KasperBaun/RabbitHouse/docs/løbegård/fundament.md

# Fundament — Løbegård

> Implementeret i `src/designs/yard/foundation.scad`.

Løbegård-fundamentet er en fundablok-ring under løbegårdens 3 ydervægge
(V1 front, V2 bag, V5 højre), lagt i **halvstensforbandt med vekslende
hjørne-ejerskab** — samme mønster som [hus-fundamentet](../hus/fundament.md).

I **kombineret build** med hus'et danner hus'ets V4-væg (ved X = 2000)
løbegårdens venstre side — så løbegårdens egen ring har KUN 3 sider. I
**standalone-build** (`standalone = true`) renderes også en venstre strip
ved X = hl så løbegården står alene.

Ringen er 4000 × 2000 mm udvendigt (yard sidder ved Y = 1000..3000 så hus'ets
front rager 1000 mm forbi yard-fronten) og 80 cm høj (4 skifter à 20 cm).
12 cm sokkel over jord, 68 cm under jord — samme dybde som hus-fundamentet.

```
        Y
        ↑
   Y=3000 ┌─────────────────────────────────────────┐  ← V2 bag (yard-segment)
          │                                         │
          │                                         │V5
          │       Løbegård X = 2000..6000           │  ← 2000 mm
          │       Y = 1000..3000                    │    (V5 højre)
          │                                         │
          │       (V4 = husets højre væg → fælles)  │
   Y=1000 └─────────────────────────────────────────┘  ← V1 front (yard-segment)
          X=2000                                X=6000
                       4000 mm
                  (V1, V2 yard-segment)
                  (set ovenfra)
```

## Mål

| Egenskab | Værdi |
|---|---|
| Løbegård-footprint udvendigt | 4000 × 2000 mm (X = 2000..6000, Y = 1000..3000) |
| Antal skifter | 4 |
| Total ringhøjde | 800 mm (4 × 200) |
| Sokkel-højde over jord | 120 mm (Z = +120 mm = RH_BASE_H) |
| Buried dybde | 680 mm |
| Fundablok dim. | 500 × 150 × 200 mm |
| Stabilgrus i bunden | 100 mm |
| Total grøftedybde | ~80 cm (680 ring + 100 grus) |
| Venstre væg (V4) | I COMBINED: ejet af hus. I STANDALONE: render egen strip |

## Halvstensforbandt — hjørner skifter ejer per skifte

Hjørnerne ved V5 (front-right og back-right) interlocker perpendikulært
mellem skifter — samme princip som hus'ets fundament, men her er det de
**lange vægge** (V1 og V2, 4000 mm) der ejer hjørnerne på ulige skifter, og
den **korte væg** (V5 — 2000 mm, fordi yard-dybden Y = 1000..3000) der ejer
hjørnerne på lige skifter.

| Skifte | Lange vægge (V1, V2 — 4000 mm) | Kort væg (V5 — 2000 mm) |
|---|---|---|
| Lige (0, 2)  | Mellem: X = 2000..5850 (8 blokke: 7×500 + 350 cut) | Fuld: Y = 1000..3000 (4 × 500) |
| Ulige (1, 3) | Fuld: X = 2000..6000 (8 × 500) | Mellem: Y = 1150..2850 (4 blokke: 3×500 + 200 cut) |

**Combined pr. skifte** = 8 + 8 + 4 = **20 blokke**.
4 skifter × 20 = **80 blokke** netto.

I STANDALONE-mode tilføjes V4 venstre væg (samme dimensioner som V5 — kort,
2000 mm): den ejer hjørner sammen med V5 på lige skifter, og sidder mellem
på ulige. Det giver 24 blokke pr. skifte × 4 = **96 blokke** standalone.

## Konstruktion — tværsnit

```
                            ↓ M10 ankerskrue c/c 1000 mm i topskiftet
        ┌────────────────────────────────────┐    ← sokkel z = +120 mm
        │            4. skifte               │
        │ - - - - - - - - - - - - - - - - -  │    ← grade z = 0 (jord/græs)
        ├────────────────────────────────────┤    ← z = −80 mm
        │            3. skifte               │
        ├────────────────────────────────────┤    ← z = −280 mm
        │            2. skifte               │
        ├────────────────────────────────────┤    ← z = −480 mm
        │            1. skifte               │
        └────────────────────────────────────┘    ← z = −680 mm
        ░░░░░░░░░ stabilgrus 100 mm ░░░░░░░░░░
        ─────────────────────────────────────    ← z = −780 mm (bund af grøft)
                       (snit gennem yard-væg)
```

Hulrum udstøbes med selvblandet beton (cement + støbemix + vand, ~1:4).
Topskiftet ligger flush med sokkel-niveau (z = +120 mm).

**Armering (Ø10 mm kamstål):**

| Placering | Antal stænger | Bemærk |
|---|---|---|
| 1. skifte (bund) | **2 stænger** vandret hele 3-sidet perimeter rundt | Lægges i hulrum før udstøbning |
| 4. skifte (top) | **2 stænger** vandret hele 3-sidet perimeter rundt | Lægges før topudstøbning, før ankerskruerne bores |
| Lodret | **4–6 stk** korte stænger (~600 mm) | I V5-hjørner + et par midt på V1/V2 — bindes til top og bund banderne |

Perimeter (3-sidet) = 4000 + 2000 + 4000 = 10 m. Per band kræves ceil(10/3) = 4
stk 3 m-stænger med overlap ~400 mm i midten af V1/V2. ALDRIG overlap i et hjørne.

M10 ankerskruer drives ned i topskiftet c/c 1000 mm. Ankeren ved X = 2000
(grænse mod hus) ejes af [hus-fundamentet](../hus/fundament.md) — yard
starter sine egne ankre ved X = 2500.

## Materialeliste — løbegård (combined mode)

| # | Vare | Beskrivelse | Antal | Enhed |
|---|---|---|---|---|
| 1 | Stabilgrus 0–32 mm | Bundlag 100 mm i frostfri grøft (~10 m perimeter × 30 cm × 10 cm) | ~0,30 | m³ (~510 kg) |
| 2 | Fundablok 50 × 20 × 15 cm | 4 skifter halvstensforbandt på 3-sidet ring (V4 er hus'ets) | 86 | stk (80 + 6 buffer) |
| 3 | Kamstål Ø10 mm × 3 m | 2 bund (8 stk for 10 m) + 2 top (8 stk). Lodrette stykker = genbrug af egne metalstænger | 16 | stk |
| 4 | Cement (Aalborg Portland CEM I/II, 25 kg-sæk) | Hulrumsudstøbning ~300 L beton ved 1:4 | 10 | sæk |
| 5 | Støbemix 0–16 mm | Sand+grus til selvblanding | ~625 | kg |
| 6 | Ankerskruer M10 × 120 | Bundrem-til-ring: 4 på V1, 4 på V2, 2 på V5 | 10 | stk |

> Priser pr. enhed slås op i [materialeliste.xlsx](../materialeliste.xlsx),
> Zone-kolonne = "Yard".

### Standalone-tillæg

Hvis løbegården bygges helt for sig selv (ingen hus), tilføj:

| Tilføjelse | Antal | Note |
|---|---|---|
| Fundablok extra | +16 stk | Venstre strip ved X = 2000 (4 skifter × 4 blokke; V4 = 2000 mm) |
| Kamstål Ø10 mm × 3 m extra | +2 stk | V4-bane: 1 bund + 1 top à 2 m (lodret = genbrug egne stænger) |
| Cement extra | +2 sæk | Ekstra hulrum (~60 L beton) |
| Stabilgrus extra | ~100 kg | Ekstra V4-grøft 2 m × 30 cm × 10 cm |
| Ankerskruer M10 extra | +2 stk | V4 venstre væg (Y = 1500, 2500) |

## Bygge-rækkefølge

1. Mark op yard-hjørner ved (2000, 0), (6000, 0), (6000, 3000), (2000, 3000).
   (Standalone: marker også ny væg-linje ved X = 2000.)
2. Udgrav rendegrøft ~30 cm bred × ~80 cm dyb langs V1 (front), V2 (bag) og
   V5 (højre). Standalone: også langs V4 (venstre).
3. Læg 100 mm stabilgrus i bunden, komprimer.
4. Læg **1. skifte** (ulige — V1, V2 ejer hjørner): V1 og V2 fuld X = 2000..6000,
   V5 mellem Y = 1150..2850. Standalone: V4 også mellem Y = 1150..2850.
5. **Læg 2 stk Ø10 mm kamstål vandret** i hulrummet i 1. skifte hele
   3-sidet perimeter rundt. Overlap ~400 mm midt på V1/V2; aldrig over hjørne.
6. Læg **2. skifte** (lige — V5 ejer hjørner): V5 fuld Y = 1000..3000. V1 og V2
   mellem X = 2000..5850. Standalone: V4 også fuld Y = 1000..3000.
7. **Sæt 4–6 lodrette Ø10 mm-stykker (~600 mm)** ned gennem hulrum i V5-
   hjørner + midt på V1, V2 — bindes til bund-banerne.
8. Læg **3. skifte** (ulige — samme som 1.).
9. Læg **4. skifte** (lige — samme som 2.).
10. **Læg 2 stk Ø10 mm kamstål vandret** i hulrummet i 4. skifte; bindes
    til de lodrette.
11. Bland beton (cement + støbemix + vand ~1:4), udstøb alle hulrum.
    Lad hærde ~7 dage.
12. Bor og sæt M10 ankerskruer c/c 1000 mm i topskiftet:
    - V1 (front): x = 2500, 3500, 4500, 5500 (4 stk; c/c 1000 fra x = 2500)
    - V2 (bag): x = 2500, 3500, 4500, 5500
    - V5 (højre): y = 1500, 2500 (2 stk; yard-dybde 2000 mm rummer kun 2)
    - Standalone V4 (venstre): y = 1500, 2500

## Rendering / verificering

```powershell
# Render combined build (hus + yard) for at se hvordan yard's fundament
# slutter op mod hus'ets V4 ved X = 2000.
& "C:\Program Files\OpenSCAD\openscad.exe" `
    -o _renders/yard_fundament.png --imgsize=1000,600 `
    --camera=3000,1500,-200,75,0,30,16000 `
    src/main.scad
```

Inspect:
- Yard's V1 og V2 starter ved X = 2000 (mod hus) og går til X = 6000
- V5 højre fundament løber fra Y = 1000 til Y = 3000 i lige skifter,
  fra Y = 1150 til Y = 2850 i ulige skifter (interlocker med V1/V2)
- I COMBINED ingen venstre væg (V4 er hus'ets); i STANDALONE er der egen V4-strip
  med samme alternation som V5
- Topskifte flush med sokkel-niveau (Z = +120 mm), 4 skifter (80 cm) dybt
- M10 ankerskruer (10 stk i combined; 12 i standalone) i topskiftet
