KasperBaun/RabbitHouse/docs/arbejdsplan/lem-og-trappe.md

# Lem & trappe — byg med det træ du har

> De to sværeste ting i gulvet. **Hvor** lemmene sidder står i
> **[gulvkonstruktion-braedder.md](gulvkonstruktion-braedder.md)** — her er **hvordan** du bygger dem.
> Hele guiden er skrevet til **genbrugstræ**: du køber ikke krydsfiner eller brede
> planker, du **måler og skærer på stedet** ud fra det du finder. Alm. gran —
> **ikke trykimprægneret**. Byg typisk **trapperne først**, lemmene til sidst.

## Kan jeg bruge dette stykke træ?

Du behøver ikke regne baglæns. Hold stykket op mod tabellen — passer det med
minimumskravet til en rolle, kan du bruge det:

| Rolle | Min. tykkelse | Min. bredde/dybde | Længde du skal bruge | Ideelt / noter |
|---|---|---|---|---|
| **Trin** | ~22 mm (helst 40–45) | **~9–10 cm** (det er trin-dybden — en fod skal kunne stå) | **55 cm** pr. trin (= trappebredden) | **Reglar 45×95 lagt fladt er perfekt.** 5 trin pr. trappe |
| **Vange** (side) | ~30 mm (helst 45) | **~95 mm** (helst 120–160 for stivhed over ~1 m) | start med **≥ 110 cm** rå, skæres til | 2 vanger pr. trappe |
| **Låg-brædt** | = gulvbræddet (~25 mm) | hvad som helst | nok til at dække åbningen | brug **rester af gulvbrædderne** så låget flugter dækket |
| **Tværrevle** (under låg) | ~30 mm | ~45 mm | passer inden for det frie hul | 2–3 pr. låg. ~45×45 er fint |
| **Fals-liste** | ~30 mm | ~45 mm | hele åbningens omkreds | ~45×45. Hyldekant låget hviler på |

Er et bræt for smalt til en vange, men tykt nok? → brug det som trin eller revle.
Intet går til spilde.

---

# DEL A — Lemmen (× 2)

Lemmen er et **udtageligt/hængslet stykke gulv** i samme tykkelse som dækket, så
den flugter. To ting afgør det: en **fals** den hviler på, og et **greb** den
løftes i. Låget bygger du selv af gulvbræt-rester — **ingen krydsfiner.**

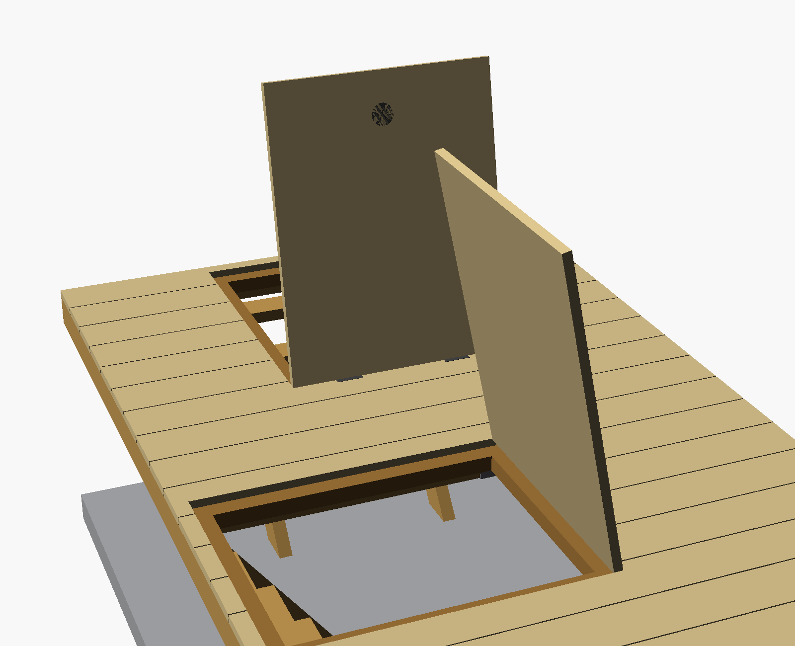
[picture p2: docs/arbejdsplan/img/lem-3d.png]
Lem — fals + greb, vist åben


*Begge låg vist åbne. Orange inderkant i åbningen = **falsen**. Ringen på
låg-oversiden = **grebet**.*

## A1 · Marker og skær åbningen

Mål fra dækkets forreste venstre hjørne (se gulv-guiden):

| Lem | Fra venstre (X) | Fra forkant (Y) | Størrelse |
|---|---|---|---|
| LEM 1 | **50,0 cm** | **4,5 cm** | 70 × 90 cm |
| LEM 2 | **75,5 cm** | **143,5 cm** | 90 × 70 cm |

1. Afsæt de 4 hjørner, slå rette vinkler med **3-4-5** (30-40-50 cm).
2. Skær med stiksav langs stregen.
3. **Tjek støtten:** hver kant skal hvile på en regel/veksel at skrue dæk + fals i.
   Mangler der støtte langs en kant (fordi bærereglarne ikke ligger som planlagt),
   så skru en **ekstra veksel 45×95** ind langs kanten først.

## A2 · Falsen — så låget ikke kan falde ned

Søm/skru **fals-liste ~45×45 hele vejen rundt på indersiden** af åbningen, med
**overkant 2,5 cm under dæk-overkant** (= i niveau med dæk-undersiden). Listen
rager ~5 cm ind og danner en hylde. Låget lægges ned i den 2,5 cm dybe fals og
**flugter dækket** — det er større end det frie hul og kan ikke falde igennem.

```
   (gulv-side)                          (åbning / kælder)
   dæk 25 ───────┐   ~0,5 cm luft  ┌─────── låg 25 mm ─────────
   z12 .........│...............│.....................  ← overkant flugter dæk
   z9,5 ────────┤▓▓▓▓▓▓▓▓▓▓▓▓▓▓│  låget hviler på falsen
   ramme-regel  │  fals-liste  │
   45×95        │ ~45×45       │
   z0  ─────────┘              └──────  ▼  frit hul ned til trappen
```

## A3 · Byg låget af gulvbræt-rester (~0,5 cm luft hele vejen)

| Lem | Åbning | **Låg (færdigt mål)** |
|---|---|---|
| LEM 1 | 70 × 90 cm | **~69,5 × 89,5 cm** |
| LEM 2 | 90 × 70 cm | **~89,5 × 69,5 cm** |

1. Læg **rester af gulvbrædderne side om side**, til de dækker åbningen, og skær
   dem så hele låget bliver ~0,5 cm mindre end åbningen i begge retninger.
2. Skru **2–3 tværrevler (~45×45) på undersiden, på tværs af bræddesamlingerne** —
   de holder brædderne sammen til ét stykke **og** afstiver mod en voksen-fod.
3. Placér revlerne **inden for det frie hul** (ikke under falsen) — så de stikker
   ned i hullet og **låser samtidig låget mod at skride sidelæns.**

## A4 · Hængsel + greb

- **2 mortiserede hængsler** så de flugter, på den angivne kant:
  **LEM 1 = bagkant (mod +Y / bagvæg)** · **LEM 2 = venstre kant (mod V3, −X)**.
- **Planforsænket klapgreb** fræset ned i oversiden i den fri kant — ingen snublekant.
- **Hold-åben strut/krog** så låget ikke kan klappe ned over dig på trappen.
- (Alternativ: helt løst lift-out-låg uden hængsler — enklere, men kan lægges forkert.)

---

# DEL B — Byg trappen (× 2)

To stejle, lige trapper ned til betonslabben — én under hver lem. Begge har
**samme mål.** Du bygger dem **mål-og-skær på stedet**: sæt vangerne efter
virkeligheden, markér trinene, skær dem til, skru fast.

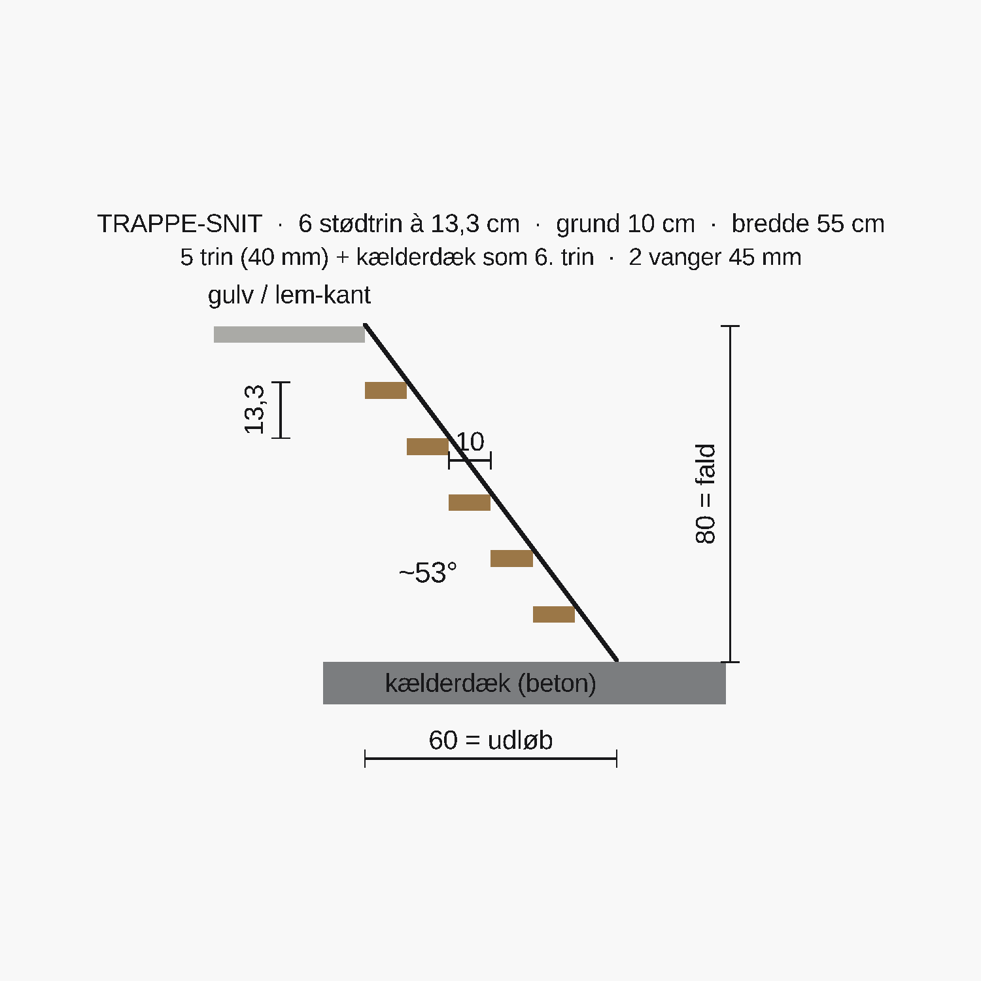
[picture p3: docs/arbejdsplan/img/trappe-snit.png]
Trappe-snit med mål


## Mål at sigte efter (begge trapper ens)

Det er **mål, ikke facit** — den endelige hældning kommer af hvor gulv og beton
faktisk står. Stemmer noget ikke, så tro på skribér-stregen, ikke tabellen.

| Størrelse | Værdi |
|---|---|
| Samlet fald (dæk → slab) | **80 cm** |
| Stødtrin (riser) | **13,3 cm** × 6 |
| Grund / trin-dybde (going) | **10 cm** |
| Trinbredde | **55 cm** |
| Vandret udløb | **60 cm** |
| Hældning | **~53°** (stejl — som en skibstrappe) |
| Trin | 5 trin + **kælderdækket som 6. trin** |

## B1 · Skær vangerne (skribér på stedet)

To vanger, én i hver side, **55 cm fra inderkant til inderkant.**

1. Tag et bræt (se mål-tabellen) på **≥ 110 cm.** Hold det skråt: **topkanten op
   under dæk-kanten ved lemmen**, **bundenden på betonslabben**, i den hældning
   trappen skal have.
2. **Tegn efter virkeligheden:** streg langs **gulvkanten foroven** og langs
   **betonen forneden.** (Du måler ingen vinkel — den bliver ~53° af sig selv.)
3. **Sav på stregerne.** Prøv at vangen sidder fladt mod både gulv og beton.
4. **Brug den færdige vange som skabelon** til vange nr. 2, så de bliver ens.

## B2 · Markér og skær trinene

1. Stil de to vanger på plads, 55 cm fra inderkant til inderkant.
2. Markér trin-overkanterne **13,3 cm lodret** mellem hvert trin (eller del faldet
   i 6 lige stykker), og **tegn en vandret streg** på indersiden af begge vanger.
   Brug vaterpas — stregen skal være vandret, ikke vinkelret på vangen.
3. Skær **5 trin på 55 cm** (= afstanden mellem vangernes inderkanter). Trin-dybden
   skal være **mindst ~10 cm** så foden kan stå — **reglar 45×95 lagt fladt** er
   perfekt.

## B3 · Skru trinene fast

- Læg hvert trin så **overkanten flugter din streg**, spændt mellem de to vanger.
- Skru **2 skruer fra ydersiden af hver vange ind i trinets ende** (4 skruer pr.
  trin). **Forbor** i vangen så enden ikke flækker; brug lange skruer (~5×80–100).
- Det **6. "trin" er selve kælderdækket** — du skærer kun 5 trin.
- Føles ét trin fjedrende når du står på det, så skru en lille klods på vangen
  under trinet — men kun hvis du mærker behov.

## B4 · Hvor hver trappe lander (mål fra samme hjørne)

| Trappe | Under | Top (øverste trin) | Går ned mod | Bund lander | Centreret |
|---|---|---|---|---|---|
| **Front-trappe** | LEM 1 | 4,5 cm fra forkant | bagvæg (+Y) | **64,5 cm fra forkant** | i bredden: trin 57,5–112,5 cm fra venstre |
| **Menneske-trappe** | LEM 2 | 165,5 cm fra venstre | mod V3 (−X) | **105,5 cm fra venstre** | i dybden: trin 151–206 cm fra forkant |

Dvs. begge trapper starter i den **lem-kant der vender væk fra rummet** og løber
60 cm ind under gulvet, mens de falder de 80 cm ned til slabben.

---

## Acceptkriterier

- [ ] Begge åbninger skåret på mål, med støtte langs alle 4 kanter.
- [ ] Fals ~45×45 hele vejen rundt, overkant 2,5 cm under dæk → låget flugter dækket og kan **ikke** falde ned.
- [ ] Låg bygget af gulvbræt-rester, ~0,5 cm mindre end åbningen, 2–3 tværrevler under, planforsænket greb (ingen snublekant).
- [ ] Hængsler mortiseret på rigtig kant (LEM 1 bagkant · LEM 2 mod V3) + hold-åben-sikring.
- [ ] Begge trapper: vanger skribéret så de står fladt mod gulv + beton, 55 cm brede, ~6 stødtrin à ~13,3 cm, 5 trin skruet fast i begge vanger, lander på slabben.
