KasperBaun/RabbitHouse/docs/arbejdsplan/skiffertag/07-sortering.md

# 7. Sortering af sten

> Skridt 7 af 10 → [oversigt](README.md). Genbrugssten sorteres på jorden,
> ALTID før oplægning — sortering "på farten" oppe på taget bliver tilfældig.

## Materialer

| Materiale | Dimension | Mængde |
|---|---|---|
| Genbrugs-naturskifer | 30×60 cm, glat 4–8 mm | ~132 i taget → køb **165 stk** |

Værktøj: skiferøkse (eller hammer til bankeprøve), 3 paller/stakke at
sortere ud på.

## Fremgangsmåde

1. **Bankeprøv HVER sten:** hold stenen løst i ét hjørne og bank med
   knoen/øksenakken. Klar klang = OK. Dødt/"skrukt" lyd = kassér.
   Håndtér stenene kontant — skjulte revner skal afsløres NU, ikke på taget.
2. Regn med **20–25 % spild** på genbrug. Frasorterede/B-sten gemmes —
   de kan blive række 1 (den skjulte bundrække) og tilskæringer (skridt 8).
3. **Gamle sømhuller:** OK hvis hullet ender skjult under overlægget (de
   øverste 90 mm af stenen). Huller i den synlige del → vend/omlok stenen,
   ellers kassér. Omlokning: nye huller lokkes **fra bagsiden**, 25–40 mm
   fra kant, to huller symmetrisk i stenens overdel.
4. **Sortér i 3 tykkelser:** tykkeste sten skal nederst ved tagfod, mellem
   på midten, tyndeste øverst mod kip.
5. **Bland sten fra flere paller/partier** løbende — giver ensartet farvespil.
6. Sten med afslåede hjørner kan bruges: det skadede hjørne vendes op under
   den overliggende sten.

## Tjek

- [ ] Alle sten bankeprøvet — ingen "skrukke" i de godkendte stakke.
- [ ] 3 stakke efter tykkelse, blandet på tværs af partier.
