KasperBaun/RabbitHouse/docs/arbejdsplan/skiffertag/08-skifer.md

# 8. Læg skifer

> **Tegninger:** [04-laegter-tegninger.html](04-laegter-tegninger.html) — pladerne set forfra, række for række, med mål.

> Skridt 8 af 10 → [oversigt](README.md). Dobbelt dækning nedefra og op,
> 7 rækker pr. tagflade. Række-positionerne er givet af lægteplanen
> ([04-laegter.md](04-laegter.md)).

**Nøgletal:**
- lægteafstand 255 mm, overlæg 90 mm (minimum ved 35°)
- pladerne er hullet **245 mm fra overkanten** → hver plade sømmes i lægten
  **under** den, dens overkant hviler på
- **2 kobbersøm 2,8×40 pr. plade**
- lodret fuge 1–5 mm — pres aldrig plader mod hinanden
- hver række forskudt **½ plade (150 mm)**
- **11 plader pr. række**

## Materialer

| Materiale | Dimension | Mængde |
|---|---|---|
| Sorterede plader (skridt 7) | 30×60 cm | 66 pr. tagflade, 132 i alt (række 7 skæres af resterne fra række 1) |
| Kobbersøm, riflet | 2,8×40 mm | ~310 brugt → 500 stk (1,5 kg) |

Værktøj: skiferøkse + fladstål (tilskæring/lokning), kridtsnor.

## Rækkerne

Mål på skråfladen fra L1's underkant. Forkanten ligger **50 mm ud forbi L1**,
så vandet lander i tagrenden.

| Række | Pladelængde | Skæres | Bund | Top | Sømmes i |
|---|---|---|---|---|---|
| 1 | **345 mm** | af **bunden**, bagside op | −50 | 295 (midt på L2) | L1 |
| 2 | 600 (hel) | — | −50 | 550 (midt på L3) | L2 |
| 3 | 600 (hel) | — | 205 | 805 (midt på L4) | L3 |
| 4 | 600 (hel) | — | 460 | 1060 (midt på L5) | L4 |
| 5 | 600 (hel) | — | 715 | 1315 (midt på L6) | L5 |
| 6 | **470 mm** | af **toppen** | 970 | 1440 (på L7) | L6 |
| 7 | **~255 mm** | **resten fra række 1** · nye huller 30 mm fra toppen | 1225 | 1480 (20 mm under kip) | L7 |

## Fremgangsmåde

1. **Række 1:** plader skåret til 345 mm — skær af bunden, så de oprindelige
   huller bliver; de rammer L1. Læg dem med **bagsiden opad**. Rækken bliver
   helt dækket af række 2. **Gem det afskårne stykke (~255 mm) — det er
   række 7.** Vælg derfor plader, hvor den *nederste* ende er pæn; den øverste
   ende må gerne være grim. Den skal være der:
   uden den løber vandet gennem fugerne i række 2. Den skal være skåret:
   række 2's søm sidder i L2, lige over række 1's overkant.
2. **Opstregning:** kridtsnor for hver 3. plade — lodret (pladebredder,
   forskudt ½ plade pr. række); vandret styrer lægterne. Læg et prøvefelt på
   ~1 m² og vurdér det, før du fortsætter.
3. **Række 2–5, hele plader, nedefra og op.** Række 2 har samme forkant som
   række 1 og starter med en halv plade. **Sømningens gyldne regel:** slå
   sømmet i, til hovedet NETOP rører pladen — pladen skal hænge på sømmene,
   ikke være spændt op. Opspænding er den klassiske årsag til revnede plader.
4. **Række 6:** skæres til 470 mm — skær af toppen, så hullerne stadig
   rammer L6. Overkanten ender på L7.
5. **Række 7:** resterne fra række 1 (~255 mm), med den originale kant
   **nedad** og snitkanten opad. Underkanten ligger 255 mm over række 6's
   underkant (1225), så toppen ender ~20 mm under kippen — det er luftspalten
   i kippen. Lok nye huller **30 mm fra overkanten**, så de rammer L7 lige
   over række 6. Sømhovederne dækkes af rygningen (skridt 10).

## Tre steder der kræver et ekstra hul eller et nip

- **Halve plader** (rækkens start/slut) har kun ét hul efter skæring — lok ét
  nyt, 245 mm fra overkanten.
- **Ved gavlene** lander det yderste søm 0–15 mm fra lægtens ende. Sæt enten
  vindskedens underbræt på først (skridt 9), eller lok et nyt hul længere inde
  på kantpladen.
- **De 10 mm:** hvert søm går kun 10 mm fri af pladen nedenunder. Er en
  genbrugsplade et par mm for lang, så nip dens øverste hjørner af.

## Tilskæring og lokning

Alle snit i denne plan ender skjult (under næste række, under rygningen eller
mod vindskeden), så det nemmeste værktøj er fint.

| Værktøj | Godt til | Bemærk |
|---|---|---|
| Vinkelsliber m. diamantskive | alle lige snit — det nemmeste | støver meget; glat, "savet" kant |
| Skifersaks / skiferklipper | mange snit, pæn brudt kant | klip **fra bagsiden** |
| Skiferøkse mod fladstål | klassisk, pæn affaset kant | kræver øvelse — regn med knækkede plader |
| Ridse og knække | tynde, ensartede plader | upålideligt på genbrugsplader |

**Med vinkelsliber:**
1. Streg snittet op på bagsiden med blyant og vinkel.
2. Læg pladen fladt på et bræt, så hele pladen er understøttet; kun det
   stykke, der skal af, stikker ud.
3. Skær i ét roligt træk uden at trykke.
4. Udendørs, med støvmaske (P3) og briller — skiferstøv indeholder kvarts.
   Lidt vand på snittet dæmper støvet.

**Hvor snittet vender:**
- Række 1: skær **bunden** af (345 mm tilbage). Resten er række 7.
- Række 6: skær **toppen** af (470 mm tilbage). Snittet dækkes af række 7.
- Række 7: snitkanten **opad**, under rygningen.
- Halve plader: snitkanten ud mod vindskeden.

**Nye sømhuller:**
- Bor med 4–5 mm murbor/flisebor **uden slag**, fra bagsiden, med pladen
  fladt på et stykke træ — eller slå hullet med skiferhammerens spids fra
  bagsiden.
- 25–40 mm fra sidekanten.
- Prøv de første snit og huller på frasorterede plader.
- En plade der ikke "falder til": flyt den til en anden række, eller hug
  et øverste hjørne af, så den lægger sig plant.
- Rækken er 11 plader + fuger. Afslut aldrig med en strimmel under 150 mm —
  tilskær i stedet de to sidste plader.

## Tjek

- [ ] Ingen opspændte søm (stikprøve: pladen kan "rasle" en anelse).
- [ ] Fuger 1–5 mm, forskydning ½ plade, ingen strimler < 150 mm.
- [ ] Forkanten 50 mm forbi L1 hele vejen — og over tagrenden.
- [ ] Ingen gamle sømhuller synlige i den færdige flade.
- [ ] Tykkeste plader nederst, tyndeste øverst.
- [ ] Ingen har betrådt den færdige dækning.
