KasperBaun/RabbitHouse/docs/arbejdsplan/skiffertag/04-laegter.md

# 4. Lægter

> **Tegninger:** [04-laegter-tegninger.html](04-laegter-tegninger.html) — lægteafstande, klodsmål og pladerne set forfra, række for række.

> Skridt 4 af 10 → [oversigt](README.md). T1-taglægter **38×73** oven på
> afstandslisterne, **255 mm fra lægte til lægte** på skråfladen.
> **Dette er det skridt, hvor præcision betaler sig** — sømmene i hver plade
> går kun 10 mm fri af pladen nedenunder.

> ⚠️ **Rækkefølge:** [stern](05-stern.md) og [tagfodsblik](06-fodblik.md)
> skal sidde, og undertaget være lagt ud over blikket, **før L1 sømmes** —
> blikket ligger under undertaget og under L1 og kan ikke skubbes ind bagefter.
> L2–L7 kan sættes uafhængigt af det.

## Materialer

| Materiale | Dimension | Mængde |
|---|---|---|
| Taglægter T1 | 38×73 mm | 14 stk à 3290 mm (køb 14 stk à 3,6 m — én længde pr. lægte, ingen stød) |
| Søm/skruer | 100 mm | 2 pr. kryds (lægte × spær) |

## Hvorfor 255 mm

Pladerne er hullet **245 mm fra overkanten** (målt på stenene, og det er
Komproments standard). En plade sømmes derfor ikke i den lægte, dens overkant
hviler på, men i **lægten under**. Sømmet skal gå fri af overkanten på pladen
nedenunder, så lægteafstanden skal være større end 245 mm. Med 255 mm går
sømmet 10 mm fri. Med den tidligere plan (225 mm) ville sømmet ramme 20 mm
nede i pladen under — det kan ikke lade sig gøre.

## Lægteplan

Alle mål er **på skrå fladen, fra L1's underkant (= spærenden) og op**. Ens
på begge tagflader. Pladens overkant ligger **midt på lægten**.

| Lægte | Underkant | Midte | Overkant | Bærer |
|---|---|---|---|---|
| L1 (tagfodslægte) | **0** | 36,5 | 73 | række 1 sømmes her |
| L2 | 258,5 | **295** | 331,5 | række 1's top · række 2 sømmes her |
| L3 | 513,5 | **550** | 586,5 | række 2's top · række 3 sømmes her |
| L4 | 768,5 | **805** | 841,5 | række 3's top · række 4 sømmes her |
| L5 | 1023,5 | **1060** | 1096,5 | række 4's top · række 5 sømmes her |
| L6 | 1278,5 | **1315** | 1351,5 | række 5's top · række 6 sømmes her |
| L7 | 1417 | 1453,5 | **1490** | række 6's top · række 7 sømmes her |

L7 sidder med overkanten 10 mm under kippen (1500).

### Klodser

Skær 3 af hver af et lægte-afkort. Stil dem på lægten under, læg næste lægte
an, søm.

| Klods | Mellem | Længde |
|---|---|---|
| A | L1 → L2 | **185 mm** |
| B | L2 → L3 → L4 → L5 → L6 | **182 mm** |
| C | L6 → L7 | **65 mm** |

## Fremgangsmåde

1. **L1:** spænd en snor mellem de to udhængsspærs ender. Et spær der stikker
   mere end ~5 mm ud forbi snoren saves tilbage; et der er for kort gør
   ingenting. Læg L1 med **underkanten på snoren** og søm den ene ende, den
   anden ende, midten — så resten.
2. Tjek L1: mål fra L1 op til kippen i begge gavle. Samme tal ±3 mm.
3. **L2–L7** med klodserne A, B og C. Sømmene går gennem lægte +
   afstandsliste ned i spæret.
4. Lægterne føres **145 mm ud forbi gavlspærene i begge ender**, samlet
   længde **3290 mm**. De sidste 145 mm hviler på afstandslisten over
   [udhængsspæret](01a-udhaengsspaer.md) — søm også dér.

## Tjek

- [ ] L1's underkant flugter spærenderne.
- [ ] Midten af L3 = **550** og midten af L6 = **1315** fra L1's underkant, i
      begge gavle (±3 mm).
- [ ] L7's overkant 10 mm under kippen.
- [ ] Planhed maks. **2 mm på 2 m retskinne** på tværs af lægterne.
- [ ] Hver lægte har søm i afstandslisten over begge udhængsspær.
