KasperBaun/RabbitHouse/docs/arbejdsplan/skiffertag/05-stern.md

# 5. Sternbrædder

> **Tegninger:** [05-stern-tegninger.html](05-stern-tegninger.html) — lav stern: snit før/nu, alle dele, rækkefølge.

> Skridt 5 af 10 → [oversigt](README.md). Ét sternbræt **25×200** på
> spærenderne ved hver tagfod — **lav stern**: overkanten flugter **spærets**
> overkant, ikke lægternes.
>
> ⚠️ **Skal op før tagfodsblikket, undertagets afslutning og L1**
> ([06](06-fodblik.md), [04](04-laegter.md)). Nummeret er historisk; rækkefølgen
> er stern → blik → undertag ud over blikket → L1.

**Hvorfor lav:** undertaget ligger på spærene. Rager sternen op over spæret,
løber vandet på undertaget ind i sternens bagside, og luften kan ikke komme
ind under L1. Med lav stern løber undertaget ud over sternens top (via
blikket), og de 25 mm under L1 står åbne som luftindtag.

**Hvorfor 200:** brættet skal dække den lodrette spærende (116 mm) +
sofitlamellen (21 mm) med margin.

## Materialer

| Materiale | Dimension | Mængde |
|---|---|---|
| Sternbrædder | 25×200 mm | 2 stk à 3390 mm (køb 2 stk à 3,6 m) |
| Skruer | 5×70 | 3 pr. spærende |

## Fremgangsmåde

1. Læg en retskinne på spærets overside, så den stikker ud over spærenden.
   Skub sternbrættet op, til dets bagkant **lige netop rører** retskinnen.
2. Skru fast med 3 skruer i hver spærende (også udhængsspærene).
3. Sternen løber **195 mm ud forbi gavlspæret i hver ende** (samlet 3390 mm),
   til vindskede-overliggerens yderside. Vindskedens brædder hakkes ned over
   sternens top i skridt 9.
4. Mal sternen sort, før blikket kommer på.
5. **Tagrende:** rendejernene skrues på sternens forside — se
   [06](06-fodblik.md).

## Tjek

- [ ] Sternens overkant i plan med spærenes overside hele vejen (retskinne).
- [ ] Sternens underkant sidder under sofitlamellernes underside — ingen
      synlig lamelkant udefra.
- [ ] Sternen rager 195 mm ud forbi gavlspæret i begge ender.
