KasperBaun/RabbitHouse/docs/arbejdsplan/skiffertag/06-fodblik.md

# 6. Tagfodsblik, fuglegitter + tagrende

> **Tegninger:** [05-stern-tegninger.html](05-stern-tegninger.html) — snit gennem tagfoden med alle dele.

> Skridt 6 af 10 → [oversigt](README.md). Tagfodsblik over den lave stern,
> ventileret fuglegitter under L1, opklodsningsliste til række 1 — og
> tagrenden, som blik og skifer skal ende i.
>
> ⚠️ **Blikket (punkt 1–2) skal på før L1.** Fuglegitter, opklodsningsliste og
> tagrende (punkt 3–5) kommer efter lægterne.

## Materialer

| Materiale | Dimension | Mængde |
|---|---|---|
| Tagfodsblik, sort/antracit | — | 2 × 3,3 m (køb 7 m) |
| Fuglegitter, ventileret, sort | — | 2 × 3,3 m (køb 7 m) |
| Opklodsningsliste, trykimp. | 10×25 mm | 2 × 3,3 m (køb 7 m) |
| Tagrende m. rendejern, endebunde og nedløb | — | 2 × ~3,4 m |
| Pappsøm/skruer | — | pr. ~300 mm |

## Fremgangsmåde

1. **Tagfodsblik:** læg blikket ~80 mm ind på spærenes overside, hen over
   sternens top og ~40 mm ned ad sternens forside med en lille drypnæse.
   Søm/skru i spærenes overside. Stød mellem blik-længder med min. 50 mm
   overlæg.
2. **Undertaget oven på blikket:** løft den flap, der hænger ud over
   tagfoden, og læg den tilbage oven på blikket, så den slutter ved sternens
   forkant. Klæb/tape kanten til blikket. Vandet løber undertag → blik →
   tagrende.
3. **Fuglegitter i gabet under L1** — de 25 mm mellem undertaget og L1's
   forkant, hele tagfoden igennem. Det er **tagets** luftindtag. Gitteret må
   ikke klemmes fladt — luften skal kunne passere op i kanalen.
   Sofittens spalter ([01b](01b-sofit.md)) er et **andet** hulrum, adskilt af
   undertaget; de har deres eget insektnet og erstatter ikke dette gitter.
4. **Opklodsningsliste 10×25** sømmes på L1 langs dens **nederste** kant. Den
   giver række 1 samme hældning som resten af taget. Række 1's søm sidder
   50 mm oppe på L1 — altså lige over listen.
5. **Tagrende:** skru rendejernene på sternens forside med fald mod nedløbet.
   Blikkets drypnæse skal ende **inde i** renden. Skiferens forkant ligger
   50 mm forbi L1 = 25 mm foran sternens forside, så hæng renden så tæt på
   sternen, som jernene tillader. Prøv med en spand vand, før skiferen lægges.

## Tjek

- [ ] Blikket ligger **under** undertaget og **over** sternens top — vand
      ledes UD, ikke ned bag sternen.
- [ ] Blikkets drypnæse ender i tagrenden i begge sider.
- [ ] Fuglegitter sidder i 25 mm-gabet under L1 i begge sider — og luften kan
      stadig passere.
- [ ] Opklodsningsliste på L1's nederste kant i begge sider.
- [ ] Tagrenden har fald mod nedløbet, og vandet løber.
