KasperBaun/RabbitHouse/docs/arbejdsplan/skiffertag/10-rygning.md

# 10. Rygning

> Skridt 10 af 10 → [oversigt](README.md). Rygningsbrædder langs kippen med
> zink-afdækning over — dækker toprækkens sømhoveder og lukker kippen.

## Materialer

| Materiale | Dimension | Mængde |
|---|---|---|
| Rygningsbrædder | 25×150 mm | 2 × 3,4 m (køb 7 m) |
| Opklodsningslister | 15 mm (rest-træ) | pr. 500 mm |
| Zink-rygning | — | 3,4 m (køb 3,5 m) |
| Skruer m. tætningsskive | — | pr. ~300 mm |

## Fremgangsmåde

1. **Rygningsbrædder:** ét bræt pr. side langs kippen, opklodset på 15 mm
   lister pr. 500 mm (så der kan ventileres under, og brættet ikke ligger
   direkte på stenene). **Dette er tagets aftræk:** de 25 mm ventilations-
   kanaler fra begge tagflader mødes i kippen mellem de to L7 og skal ud herigennem.
   **Lad rygningens ender ved gavlene være åbne** — luk dem ikke af med kit
   eller træ, ellers står luften stille i hele tagfladen.
2. **Zink-rygningen** lægges over og skrues med tætningsskiver i
   rygningsbrædderne — aldrig gennem stenene.
3. Naturskifer holdes **~5 mm fri** af zinken (stenene må ikke bære på
   metallet).
4. Zinken løber gavl til gavl og ender mod vindskede-overliggerne. Den må
   gerne lukke tæt ovenpå — luften går ud gennem **15 mm-spalten under
   rygningsbrædderne**, så den spalte skal være fri hele vejen ud til
   gavlene.

## Tjek

- [ ] 15 mm-spalten under rygningsbrædderne er fri hele vejen ud til begge
      gavle — fri luftvej fra tagfod til kip.
- [ ] Alle toprækkens sømhoveder ligger skjult under rygningen.
- [ ] Zink fastgjort i brædderne med tætningsskiver — ingen skruer i sten.
- [ ] Enderne lukker pænt mod overliggerne ved begge gavle.
