KasperBaun/RabbitHouse/docs/arbejdsplan/skiffertag/01a-udhaengsspaer.md

# 1a. Udhængsspær + klodser (gavludhæng)

> **Tegninger:** [01a-udhaengsspaer-tegninger.html](01a-udhaengsspaer-tegninger.html) — indkøb, skæreplan, klodsplacering, snit.

> Hører til trin 1, umiddelbart efter [spærene](01-spaer.md) er rejst og loddet.
> Ét ekstra spær pr. gavl — sat **145 mm ude forbi gavlspæret og i nøjagtig
> samme plan** — holdt på plads af klodser ind til gavlspæret.

## Hvorfor

Gavludhænget blev oprindeligt båret alene af de udkragede **taglægter**. Men
lægterne ligger 28 mm (undertag 3 + afstandsliste 25) **over** spærplanet, og
derfor kan de hverken bære undertaget eller en sofit. Konsekvensen var at

- undertaget måtte stoppe ved gavlspæret, så vand på banen løb ind bag
  gavlbeklædningen i stedet for ud over kanten, og
- gavludhængets underside stod åben — man kunne kigge lige op i lægterummet
  fra siden, og tagskægget var kun lukket ved de to tagfødder.

Udhængsspæret lægger træ **i spærplanet** hele vejen ud til vindskeden. Så kan
undertaget føres helt ud, gavlsofitten kan sømmes op i samme plan som
tagfods-sofitten (hjørnerne mødes), lægterne får anlæg i spidsen i stedet for
at krage frit, og vindskedens underbræt får fæste i både lægte- **og**
spærender.

## Materialer

| Materiale | Dimension | Mængde |
|---|---|---|
| Konstruktionstræ C24 (samme emne som spærene) | 45×95 mm | 4 udhængsspær à 1500 mm → **2 stk à 3,6 m** |
| Klodser | 45×95 mm | 12 stk à 100 mm — skæres af de 2 × 600 mm afkort, intet ekstra køb |
| Skruer | 5,0×80 | 48 stk (4 pr. klods: 2 i gavlspæret, 2 i udhængsspæret) |
| Hulplade/samlebeslag over kipstødet | ~40×200 | 2 stk (1 pr. gavl) |

Udhængsspæret er **nøjagtig samme emne som de 12 spær**: parallelogram, 1500 mm
langs kanten, 35° gering i begge ender. Brug samme skabelon — der skal ikke
regnes om, og der skal ikke skråskæres noget.

Klodserne er **firkantkappede afkort**. De skal ikke tilpasses tagfladen: de
sidder mellem to spær og er kun afstandsholder + sømfæste, så en almindelig
lodret kapning er nok (sæt overkanten efter klodsens laveste hjørne, så den
aldrig kan stikke op gennem spærplanet).

## Placering

Positionerne er **skråmål fra spærenden**, ens på begge halvtage og i begge
gavle:

| Klods | Skråmål fra spærende |
|---|---|
| K1 | 150 mm |
| K2 | 700 mm |
| K3 | 1250 mm |

```
   SNIT VED GAVL (set på tværs af huset)

           lægte 38x73                    ← krager 145 ud, lander nu
          ┌────┐                            på afstandslisten
    ══════╧════╧═══════════  undertag     ← føres helt ud
    ┌──────────┬─────┬──────────┐
    │ UDHÆNGS- │KLODS│ gavlspær │  alle 45x95, overkanter flugter
    │  SPÆR    │ 100 │          │
    └──────────┴─────┴──────────┘
    ▬▬▬▬▬▬▬▬▬▬▬▬▬▬▬▬▬            sofit-lameller (trin 1b)
    │←─ 145 ─→│← beklædning
    │
    vindskede sømmes på BÅDE lægte- og udhængsspær-ender (trin 9)
```

## Fremgangsmåde

1. **Kap 4 udhængsspær** på spær-skabelonen (1500 mm, 35° i begge ender).
   Der er **ingen fugleudskæring** — udhængsspæret hviler ikke på topremmen.
2. **Kap 12 klodser** à 100 mm af 45×95.
3. Skru de 3 klodser fast på gavlspærets yderside i K1/K2/K3, med **klodsens
   overkant lige under spærets overkant** (aldrig over — så bærer klodsen
   undertaget forkert). 2 skruer 5,0×80 pr. klods.
4. Læg udhængsspæret op mod klodsernes yderside og skru igennem. Kontrollér
   med en retskinne hen over gavlspær → udhængsspær at **overkanterne
   flugter**: det er den flade undertag og lægter skal ligge på.
5. De to halvdele mødes i kippen med samme lodrette stødsnit som spærene.
   Sæt en hulplade over stødet på ydersiden — hanebåndet mangler her.
6. Gentag i den anden gavl.

## Tjek

- [ ] Retskinne fra gavlspær ud over udhængsspær: **ingen spring** i overkanten,
      hele vejen fra tagfod til kip, i begge gavle.
- [ ] Udhængsspærets yderside står **145 mm** fra gavlspærets yderside — mål i
      begge ender og på midten (samme mål som lægternes udkragning).
- [ ] Klodserne stikker ikke op over spærplanet.
- [ ] Kipstødet er samlet med beslag i begge gavle.
