KasperBaun/RabbitHouse/docs/arbejdsplan/skiffertag/01-spaer.md

# 1. Spær

> Skridt 1 af 10 → [oversigt](README.md). 6 spærfag med hanebånd, hældning 35°.
> Målsatte tegninger: [01-spaer-tegninger.html](01-spaer-tegninger.html) (åbn i en browser).

## Materialer

| Materiale | Dimension | Mængde |
|---|---|---|
| Konstruktionstræ C24 | 45×95 mm | 12 spær à 1,5 m + 6 hanebånd à 0,94 m (køb 9 stk à 3,6 m: 6 længder à 2 spær + 2 længder à 3 hanebånd + 1 i reserve) |
| Vinkelbeslag + beslagskruer 4,0×40 | 90×90×40 | 12 stk (2 pr. fag) |
| Skruer til hanebånd | 5,0×80 | 24 stk (4 pr. samling, 2 samlinger pr. fag) |

## Skæremål

Geometri: hældning 35°, kip ved 1000 mm fra vægydersiden, udhæng 229 mm vandret.

| Emne | Antal | Længde | Endesnit |
|---|---|---|---|
| Spær 45×95 | 12 | **1500 mm** målt langs kanten (over- og underkant er lige lange) | Gering **35°** i begge ender, snittene **parallelle** — emnet er et parallelogram |
| Hanebånd 45×95 | 6 | overkant **667 mm** / underkant **938 mm** | Gering **55°** i begge ender, spejlvendt — emnet er et trapez (går saven kun til 45–50°: afsæt de to kantmål, tegn stregen og skær med rundsav/håndsav) |

**Hanebåndets placering** (til skabelonen på jorden): overkantens endepunkt
rammer spærets underkant **407 mm fra kipsnittet målt langs underkanten**
(svarer til overkant 467 mm over topremmen, når faget står rejst).

**Fugleudskæring** (afsættes på plads, jf. pkt. 2):

- Hælsnittet (det lodrette snit) sidder hvor spærets underkant rammer
  topremmens yderkant — **280 mm fra fodenden målt langs underkanten**
  (= 229 mm vandret udhæng). Fra mærket: lodret hælsnit **38 mm** op,
  vandret sæde **55 mm** ind mod kip.
- Det giver ~32 mm dybde vinkelret på spæret = maks 1/3 af spærhøjden
  (95 mm). Hælen ligger an mod topremmens yderside, sædet hviler på
  oversiden. Sav alle 12 udskæringer med samme dybde — ellers bølger
  tagfladen.

## Fremgangsmåde

1. **Byg ét fag på jorden som skabelon.** To spær 45×95: kip-enden kappes
   **lodret** (geringssav på 35°), fod-enden lades lang (teoretisk
   færdiglængde 1500 mm, se skæremål) — spærene mødes i kip med et lodret
   stødsnit, INTET kipbræt/rygningsplanke.
2. **Fugleudskæring:** læg faget op på plads (eller mål ud) og mærk hvor
   spærets underkant rammer topremmens yderkant. Sav et sæde (vandret snit
   55 mm + lodret snit 38 mm, se skæremål), så spæret hviler plant på
   topremmen. Kap derefter fodenden lodret 280 mm (langs underkanten) uden
   for hælmærket — spærfoden rager så **229 mm ud forbi væggen**
   (tagudhænget).
3. **Hanebånd 45×95:** monteres med **overkant 467 mm over topremmens
   overside**, ender kappet så endefladen ligger plant an mod spærets
   underside (overkant 667 / underkant 938 mm, se skæremål). 4 skruer
   pr. ende.
4. Byg de øvrige 5 fag oven på skabelonen, så alle er ens.
5. **Rejs fagene** — forkant af faget ved Y = 0 / 600 / 1200 / 1800 / 2400 /
   2955 mm målt fra frontvæggens (V1) yderside. Gavl-fagene flugter
   **indersiden** af V1 og V2. Lod hvert fag op og afstiv midlertidigt med
   skråbrædder.
6. Fastgør hvert spær til topremmen med vinkelbeslag (+ skråsøm fra den
   anden side).

## Næste

Når fagene står: [1a — udhængsspær + klodser](01a-udhaengsspaer.md). De skal
op **før** undertaget, ellers kan banen ikke føres ud i gavludhænget.

## Tjek

- [ ] Alle 6 fag i lod og flugt — snor over kip-punkterne er en ret linje.
- [ ] Spærfødder rager 229 mm ud i begge sider.
- [ ] Fugleudskæringer ligger plant an; ingen vipper.
