KasperBaun/RabbitHouse/docs/arbejdsplan/skiffertag/01b-sofit.md

# 1b. Sofit under tagskægget — hele vejen rundt

> Hører til trin 1, efter [udhængsspærene](01a-udhaengsspaer.md) og før
> [undertaget](02-undertag.md). Ventilerede lameller sømmet op under
> spærene, **på alle fire tagskæg**: begge tagfødder (spærenderne krager
> 229 mm ud) og begge gavle (udhængsspærene krager 145 mm ud).

## Hvorfor lameller og ikke krydsfiner

Sofitten var tidligere tænkt som 18 mm udvendig krydsfiner — en tæt plade.
Den er valgt fra: pladen er dyr i småstykker, kanterne suger vand, og den
lukker tagskæggets eget hulrum helt af, så fugt fra spærenderne ikke kan
komme væk. I stedet: **høvlet forskalling m/fas i smalle lameller med luft
imellem** — den kan købes i almindelig længde hos jem & fix, den følger
35°-hældningen uden at skulle rippes, og spalterne lufter hulrummet.

> **Vigtigt:** spalterne lufter **tagskæggets** hulrum (mellem sofit og
> undertag), ikke selve tagkonstruktionen. Tagets ventilation løber fortsat i
> de 25 mm mellem afstandslisterne, under lægterne, med indtag ved
> [fodblikket](06-fodblik.md) og aftræk ved rygningen. De to hulrum er adskilt
> af undertaget og skal ikke forveksles.

## Materialer

| Materiale | Dimension | Mængde |
|---|---|---|
| Høvlet forskalling m/fas, gran (jem & fix 25×50, **høvlet mål 21×45**) | 21×45 mm | ~45 m brugt → **22 stk à 2,4 m** (~370 kr) |
| Insektnet, rustfrit/alu, maskevidde ≤ 2 mm | 300 mm bredt | ~7 m til tagfødderne + ~6 m i 100 mm bredde til gavlene |
| Skruer, rustfri/varmforzinket | 4,0×40 | ~2 pr. lamel pr. spær |
| Hæfteklammer, rustfri | — | til nettet |

Forbrug: tagfod 2 × 5 lameller à 3290 mm = 32,9 m; gavl 4 × 2 lameller à
1500 mm = 12,0 m. I alt 44,9 m + stød/spild.

> REQ-008's krav om svejst trådnet ≤ 25 × 13 mm gælder **rummets** afgrænsning
> mod rovdyr — sofitten sidder uden for den (over topremmen). Nettet her er
> mod fugle, hvepse og mus i tagskægget; derfor et fint net, ikke volierenet.

## Lamelplan

Lamellerne ligger **parallelt med tagkanten**, så hver lamel krydser og får
fæste i hvert eneste spær. Spalten fordeles jævnt, så yderste lamel flugter
sternen/vindskeden og inderste flugter væggen.

| Tagskæg | Bredde at lukke | Lameller | Spalte |
|---|---|---|---|
| **Tagfod** (2 stk) | 280 mm skråmål (229 vandret / cos 35°) | 5 stk à 3290 mm, langs tagfoden | **13,5 mm** |
| **Gavl** (4 stk, ét pr. halvtag) | 97 mm (145 udhæng − 48 mm beklædning) | 2 stk à 1500 mm, op ad skråfladen | **7 mm** |

Ved gavlen sidder den **yderste** lamel under udhængsspæret (fuldt anlæg) og
den **inderste** under klodserne (K1/K2/K3). Ved tagfoden sømmes alle 5
lameller op i hver spærunderside.

```
   TAGFOD, snit                     GAVL, snit
   (5 lameller op ad skråfladen)    (2 lameller på tværs)

   væg ─┐                            beklædning ─┐
        │▬▬ ▬▬ ▬▬ ▬▬ ▬▬│ stern            │▬▬ ▬▬│ vindskede
        └── 280 mm ────┘                  └ 97 ─┘
         ↑  ↑  ↑  ↑                        ↑  ↑
       13,5 mm spalter                    7 mm spalte
```

## Fremgangsmåde

1. **Sæt nettet først.** Hæft insektnettet på lamellernes overside (eller
   direkte op under spærene, hen over hele udhænget) *inden* lamellerne skrues
   op — bagefter kan man ikke komme til. Overlæg ved stød.
2. **Start yderst** ved sternen/vindskeden og arbejd ind mod væggen, så den
   yderste lamel flugter rent — resten af unøjagtigheden lander i den inderste
   spalte, hvor den ikke ses.
3. **Skru op i hver spærunderside**, 2 skruer pr. krydsning. Stød mellem to
   lameller placeres **midt på et spær**, så begge ender har fæste — og
   forskyd stødene, så de ikke ligger i samme spærfag.
4. **Hjørnerne:** gavl-lamellerne løber ubrudt hen over tagfodshjørnet (fra
   spærende til spærende), og tagfods-lamellerne støder ind mod dem. Så bliver
   hjørnet lukket uden gering.
5. Mal lamellerne **før** montage (huset er sortmalet) — kanterne og fasen er
   umulige at nå bagefter.

## Tjek

- [ ] Sofit på **alle fire** tagskæg — begge tagfødder og begge gavle.
- [ ] Insektnet bag hver eneste spalte, uden huller ved stød og i hjørnerne.
- [ ] Spalterne er jævne — ingen enkeltspalte over ~15 mm.
- [ ] Stød ligger over et spær, ikke i luften, og er forskudt.
- [ ] Yderste lamel flugter sternens/vindskedens inderside; sternen (25×200)
      dækker lamellens kant udefra.
