KasperBaun/RabbitHouse/docs/arbejdsplan/skiffertag/02-undertag.md

# 2. Undertag

> Skridt 2 af 10 → [oversigt](README.md). Diffusionsåbent banevareundertag
> direkte på spærene (OK ved 35° — banevare kræver min. 25°).

## Materialer

| Materiale | Dimension | Mængde |
|---|---|---|
| Undertag, diffusionsåbent (banevare) | — | ~10 m² brugt (2 × 1500 × 3290) → 1 rulle |
| Hæfteklammer / pappsøm | — | — |

## Fremgangsmåde

1. Rul banerne **vandret**, nederste bane først, nedefra og op. Overlæg
   mellem baner efter rullens anvisning (typisk 100–150 mm).
2. Ved **tagfod**: før undertaget ud over spærenderne, så vand på undertaget
   ledes ud til drypkanten (fodblikket monteres i skridt 6 og tager over).
3. Ved **gavlene**: før undertaget **helt ud over udhængsspæret** og kap det i
   flugt med dets yderside (145 mm forbi gavlspæret). Så drypper vand på banen
   fri af vindskeden i stedet for at løbe ind bag gavlbeklædningen.
   Det forudsætter at [udhængsspærene](01a-udhaengsspaer.md) er sat — uden dem
   ligger der intet træ i spærplanet derude, og banen ville hænge frit.
4. Ved **kip**: sidste bane føres hen over kippen til den anden side, så
   kippen er lukket.
5. Hæft kun i spær-toppene (klammer/pappsøm) — afstandslisterne i næste
   skridt klemmer banen permanent fast.
6. Undertaget må gerne hænge en anelse mellem spærene (lille lunke leder
   vand mod tagfod), men uden folder på tværs.

## Tjek

- [ ] Overlæg vender rigtigt (øverste bane over nederste) hele vejen.
- [ ] Ført ud over spærenderne ved begge tagfødder; ført ud over
      udhængsspærene ved begge gavle; lukket over kip.
- [ ] Banens bredde måler **3290 mm** (3000 + 2 × 145) fra gavlkant til gavlkant.
- [ ] Ingen huller/flænger — små skader tapes med undertagstape.
