KasperBaun/RabbitHouse/docs/arbejdsplan/skiffertag/03-afstandslister.md

# 3. Afstandslister

> Skridt 3 af 10 → [oversigt](README.md). 25×50 trykimprægnerede lister oven
> på undertaget, langs hvert spær — **også de to udhængsspær**. De klemmer
> undertaget fast og løfter lægterne, så vand på undertaget kan løbe frit ned
> til tagfoden.

## Materialer

| Materiale | Dimension | Mængde |
|---|---|---|
| Afstandslister, trykimp. | 25×50 mm | 16 stk à 1,5 m — 12 over spærfagene + 4 over udhængsspærene (køb 26 m) |
| Søm/skruer | 75 mm | ~5 pr. liste |

## Fremgangsmåde

1. Én liste **midt over hvert spær** (8 pr. tagflade: 6 spærfag + 2
   udhængsspær), fra spærende til kip, hele skråfladen.
   Listen over et **udhængsspær** kappes i flugt med spærets yderside i stedet
   for at ligge centreret — ellers stikker den 2,5 mm ud i vindskeden.
   Den er vigtig: det er dén, lægternes udkragede ender lander på.
2. Søm/skru gennem liste + undertag ned i spæret, ca. pr. 300 mm.
3. Listerne må gerne stødes på langs — stød behøver ikke ligge over noget
   særligt, de bærer kun lægterne lokalt.

## Tjek

- [ ] Liste over ALLE spær på begge tagflader, inkl. udhængsspærene (2 × 8 stk).
- [ ] Listen over udhængsspæret flugter spærets yderside — den må ikke stikke ud.
- [ ] Undertaget ligger glat under listerne — ingen folder klemt fast.
