KasperBaun/RabbitHouse/docs/arbejdsplan/skiffertag/09-vindskeder.md

# 9. Dobbelt vindskede

> Skridt 9 af 10 → [oversigt](README.md). To brædder oven på hinanden langs
> begge skrå gavlkanter: **underbræt 25×200** på lægte- og udhængsspær-enderne
> + **overligger 25×150**, der rager op over skiferfladen og lukker tagkanten
> mod vind. Underbrættet er lige så højt som sternen, så underkanterne flugter
> i tagfodshjørnet og dækker sofitlamellens kant.

## Materialer

| Materiale | Dimension | Mængde |
|---|---|---|
| Underbrædder | 25×200 mm | 4 stk à ~1,9 m (køb 8 m) |
| Overliggere | 25×150 mm | 4 stk à ~1,9 m (køb 8 m) |
| Skruer | 5,0×70 | 3–4 pr. bræt |

## Fremgangsmåde

1. **Underbræt** sømmes på **både lægte-enderne og udhængsspærets endetræ**,
   overkant presset op mod skiferens underside. Skiferen ligger ud over
   underbrættets overkant og ender i flugt med dets yderside. Underkanten
   lander ~19 mm under gavlsofittens underside og dækker dens kant.
2. **Overligger** skrues uden på underbrættet, forskudt opad så det rager
   **~40 mm op over skiferfladen**.
3. Ved kippen mødes brædderne fra de to tagflader i et lodret stød.
4. **Nederste ender** føres ud over sternens endetræ og skæres **lodret i
   flugt med sternens forside** og **vandret** (underbrættet i flugt med
   sternens underkant), så hjørnet lukker uden spring.

## Tjek

- [ ] Overligger rager jævnt ~40 mm op over skiferen hele vejen.
- [ ] Hjørner mod stern lukker uden spring; sternens endetræ er dækket.
- [ ] Underbrættet dækker gavlsofittens yderkant hele vejen op mod kippen.
- [ ] Ingen sten er knækket under montagen (der arbejdes over færdig dækning
      — læn aldrig noget mod stenene).
