KasperBaun/RabbitHouse/arbejdsplan.md

# Arbejdsplan — Kaninhus

Trin i byggerækkefølge, grupperet pr. byggesystem. Hus-zonen (X = 0..1500).
Løbegården er en separat struktur og står til sidst.

## 0. Forberedelse & opmåling ✅

- [x] Vælg + ryd placering, ret terræn af
- [x] Mål op, sæt galger og snor (2000 × 3000 mm)
- [x] Marker hjørner ved (0,0), (2000,0), (2000,3000), (0,3000)
- [x] Afsæt grøftebredde til udgravning

## 1. Fundament ✅

- [x] Udgrav rendegrøft ~30 cm bred × ~80 cm dyb
- [x] Stabilgrus 100 mm i bund, komprimer
- [x] Læg fundablok-ring, 4 skifter halvstensforbandt
- [x] Vandret armering bund + top, lodret i hjørner
- [x] Udstøb hulrum med beton, lad hærde
- [x] Sokkelpuds på blokke. Kontroller om hele fundamentet er vandret, og ret evt. af med mørtel inden pudsning.
- [x] Støb klaplag i fundamentets indre.

## 1b. Dræning & fugtsikring (efterbygning) → [draening.md](docs/hus/draening.md)

Kælderen står med vand året rundt. Der blev aldrig projekteret dræn,
kapillarbrydende lag, fugtspærre eller ventilation under terræn.
Klaplaget fra trin 1 brydes op og erstattes.

- [ ] Prøvehul 1,2 m + plastfolieprøve + skyd afløbskoten — beslut løsning eller Plan B
- [ ] Tagrender + nedløb til sandfangsbrønd (**før** graven åbnes)
- [ ] Omfangsdræn: smøremembran + grundmursplade + Ø92 dræn i kote −1000/−1050, fag à maks. 1,0 m
- [ ] Rense-/sandfangs-/pumpebrønd + afløb med 3–5 ‰ fald
- [ ] Nyt kældergulv: opsamlingsdræn, 150 mm singels, radonspærre, støbning m. fald 1:100
- [ ] Ventilation: 4 × sokkelrist à 150 cm² + grusskørt, net 13 mm + insektnet
- [ ] Murpap mellem reglar og sokkel; trykimprægneret trappe
- [ ] Terrænregulering 1:50 væk fra alle 4 vægge + lerlåg over rendens tilfyldning

## 2. Gulv 

- [x] Gulv konstruktion (reglar + gulvbrædder) → [gulvkonstruktion-braedder.md](docs/arbejdsplan/gulvkonstruktion-braedder.md)
- [x] Lemme og trapper ned i kælder → [lem-og-trappe.md](docs/arbejdsplan/lem-og-trappe.md)

## 3. Konstruktions-skelet (vægge)

- [x] Monter bundrem, murpap og ankerbolte → [detaljer](docs/arbejdsplan/bundrem-murpap-ankerbolte.md)
- [x] Rejs V3 (venstre)
- [x] Rejs V1 (front, m. dør-åbning — ingen vinduer i facaden)
- [x] Rejs V2 (bag)
- [x] Rejs V4 (partition, m. hus-dør + pet-dør)
- [x] Læg topremme på alle 4 vægge
- [x] Vinkelbeslag i alle hjørner

## 4. Tagkonstruktion

- [x] Rejs spær m. hanebånd + fugleudskæring → [01-spaer.md](docs/arbejdsplan/skiffertag/01-spaer.md)
- [ ] Udhængsspær + klodser ved begge gavle → [01a-udhaengsspaer.md](docs/arbejdsplan/skiffertag/01a-udhaengsspaer.md)
- [ ] Sofit under tagskæg — **alle 4 sider**, ventilerede lameller → [01b-sofit.md](docs/arbejdsplan/skiffertag/01b-sofit.md)

## 5. Tagdækning (skifer) → **[BYGGEPLAN: nøglemål, lægteplan + indkøbsliste](docs/arbejdsplan/skiffertag/README.md)**

> Næste skridt er **lægtning (4)**. Læs "Gør dette FØR du køber og skærer" i
> byggeplanen først — der er tre ting at måle inden der bestilles sten og søm.

- [x] Undertag → [02-undertag.md](docs/arbejdsplan/skiffertag/02-undertag.md)
  - [ ] forlæng banen ud over udhængsspærene i begge gavle (3290 mm bred)
- [x] Afstandslister 25×50 over spær → [03-afstandslister.md](docs/arbejdsplan/skiffertag/03-afstandslister.md)
  - [ ] eftermontér de 4 lister over udhængsspærene
- [ ] Lægtning 38×73, 255 mm (stern + tagfodsblik først, så L1) → [04-laegter.md](docs/arbejdsplan/skiffertag/04-laegter.md)
- [ ] Sternbrædder ved begge tagfødder → [05-stern.md](docs/arbejdsplan/skiffertag/05-stern.md)
- [ ] Tagfodsblik + fuglegitter + opklodsningsliste + tagrende → [06-fodblik.md](docs/arbejdsplan/skiffertag/06-fodblik.md)
- [ ] Sortér genbrugssten → [07-sortering.md](docs/arbejdsplan/skiffertag/07-sortering.md)
- [ ] Læg skifer (række 1 → 7) → [08-skifer.md](docs/arbejdsplan/skiffertag/08-skifer.md)
- [ ] Dobbelt vindskede ved gavle → [09-vindskeder.md](docs/arbejdsplan/skiffertag/09-vindskeder.md)
- [ ] Rygning → [10-rygning.md](docs/arbejdsplan/skiffertag/10-rygning.md)

## 6. Udvendig beklædning

- [x] Vindpapir på alle vægge, stift c/c 200
- [x] Cut åbninger i vindpapir
- [x] Afstandslister c/c 600
- [x] Beklædning (klink) — sortmalet; V4 mangler stadig omkring hus-dør-åbningen
- [x] Hjørnetrim ved 4 hjørner

## 7. Åbninger

- [x] Hoveddør V1 — karm 948 × 2050 sat i lysning 968 × 2047, krydsfinerblad
      med rombe-udskæring (240 × 280, foring ~45), 2 båndhængsler + greb/cylinder
- [x] Side-vindue V3 — to-rammet vindue i lysning 860 × 1000, sål 955 over gulv
- [ ] Rude i dørbladets rombe (står åben lige nu)
- [ ] Indvendig hus-dør V4 (Å2)
- [ ] Kattelem i pet-åbning
- [ ] Yard-udhusdør (Å1, mesh-leaf)

## 8. Isolering

- [ ] Mineraluld i væg-cavity
- [ ] Dampspærre
- [ ] Isoler gulv mellem strøer (valgfrit)

## 9. Indvendig beklædning

- [ ] Plader indvendigt på vægge

## 10. Inventar

- [ ] Rede-kasse
- [ ] Høhæk
- [ ] Foder-/vandskåle

## 11. Overfladebehandling

- [ ] Træbeskyttelse/maling udvendigt
- [ ] Behandling indvendigt
- [ ] Slut-rengøring + indflytning

---

## Løbegård (separat struktur)

- [ ] Fundament
- [ ] Skelet (V5 + V1/V2-segmenter)
- [ ] Voliere-net (front + bag + højre)
- [ ] Yard-dør
- [ ] Tag-låg (mesh)
