KasperBaun/RabbitHouse/docs/skaereliste-skelet.md

# Skæreliste — Konstruktions-skelet

> **Flyttet.** Pr-væg skærelister bor nu i zone-doc'ene sammen med ASCII
> elevation og materialeliste — så du kun behøver åbne én fil pr. enhed.

| Zone | Doc |
| --- | --- |
| Hus | [hus/konstruktions-skelet.md](hus/konstruktions-skelet.md) |
| Løbegård | [løbegård/konstruktions-skelet.md](løbegård/konstruktions-skelet.md) |
