KasperBaun/RabbitHouse/docs/hus/skaereliste/00-oversigt.md

# Hus — skæreliste & væg-tegninger

Save-og-mål-guide for husets 4 vægge. Alle mål i mm. Én tegning pr. væg:
[V1 front](V1-front.md) · [V2 bag](V2-bag.md) · [V3 venstre](V3-venstre.md) · [V4 partition](V4-partition.md)

## Plan (set ovenfra)

```
              V2 — bag  (Y=3000)
          ┌───────────────────────────┐
   V3 ────│                           │──── V4  (partition, X=2000)
 venstre  │        2000 × 3000        │      hus-dør + pet-dør
  (X=0)   │                           │
sidevindue└───────────────────────────┘
              V1 — front  (Y=0)
        X=0    kun dør, ingen vinduer   X=2000
```

## Sådan måler du (datum)

```
  terræn → fundablok-ring TOP = 120 → DPC 2 → BUNDREM-TOP = 167  ← NULPUNKT
         → stud 2000 → TOPREM-TOP = 2212
```

I væg-tegningerne er **højder målt fra bundrem-overkant (h=0)** og **vandret fra
venstre/nedre hjørne (=0)**. Hægt tape i hjørnet og på bundremmen og sæt af.

## Indkøb (45×95 reglar)

| Materiale | Bruges til | ≈ løbende m |
| --- | --- | --- |
| 45×95 PT NTR-AB | Bundrem (2×2000 + 2×2810) | 9,6 |
| 45×95 gran/C24 | Toprem (2×2000 + 2×2810) | 9,6 |
| 45×95 C24 | 22 studs à 2000 | 44,0 |
| 45×95 C24 | Headers, sål, cripple (V3-sidevindue + V4 pet-dør) | 3,0 |

**I alt 45×95 C24/gran ≈ 57 m + bundrem PT ≈ 10 m.** Studs er ens 2000 mm på
alle vægge. Dørene går fra sokkel-/gulvniveau op til toprem-underkant, så
topremmen er dør-header (ingen cripple over dørene) — og V3-vinduets header
flugter ligeledes topremmen, så der heller ikke er cripple over vinduet.
På V1 er bundremmen skåret væk under døren (2 × 516 i stedet for 2000).

## Bygge-rækkefølge

1. DPC på ringen → læg **bundrem** (bor M10 c/c ~1000, spænd ankerskruer).
2. Rejs **V3** (venstre) m. sidevindue-ramme (lysning 860×1000) → toprem.
3. **V1** (front) m. dør-ramme (lysning 968×2047) → toprem. Ingen vinduer.
4. **V2** (bag) → toprem.
5. **V4** (partition) m. dør-rammer → toprem.
6. **Vinkelbeslag** i alle 4 hjørner (top + bund).
