KasperBaun/RabbitHouse/docs/arbejdsplan/img/gulv-plan.png

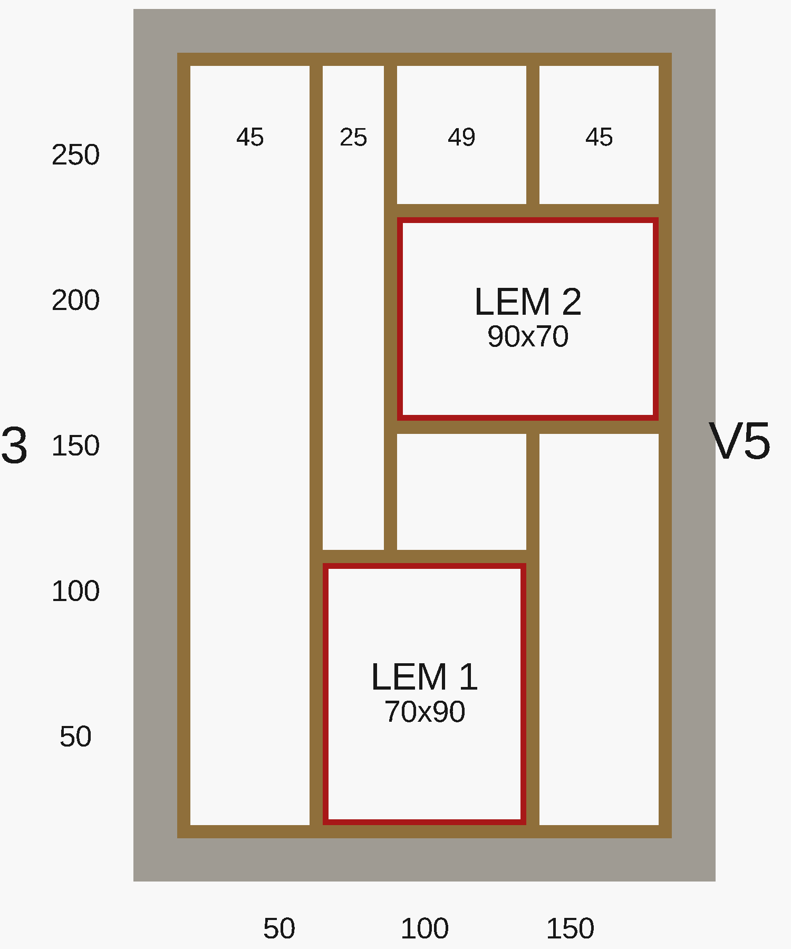
docs/arbejdsplan/img/gulv-plan.png
