KasperBaun/RabbitHouse/docs/media/oplaegning-300x600.png

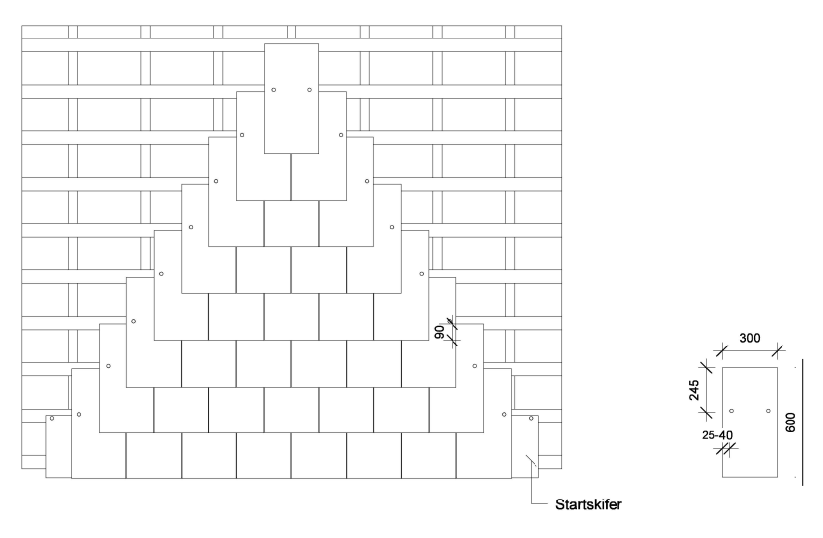
docs/media/oplaegning-300x600.png
