KasperBaun/RabbitHouse/src/designs/house/roof.scad

// HOUSE roof dispatcher.
//   Gable covers ("skifer"): spær/vindskeder live in roof_gable.scad; this
//   file adds the sternbrædder at both eaves and exposes step-by-step
//   entries (RenderHouseRoofSpaer / -Stern / -Vindskeder) matching the
//   arbejdsplan work steps.
//   Mono-pitch covers (tagpap/eternit): legacy path — rafters X<=1200 +
//   left-side lookouts + fascia/soffit, all helpers in this file.
// Cover layers are shared and live in designs/roof_plates*.scad.

include <../../lib/defaults.scad>
include <../config.scad>
use <../../lib/primitives/beslag.scad>
use <roof_gable.scad>

SOFFIT_T = 18;   // legacy mono-pitch soffit: 18 mm krydsfiner (se _soffit_panel)

// Sofittens inderkant ved gavlene = klink-beklædningens yderside; derude
// stopper gavltrekantens beklædning netop i spærplanet, så lamellerne lapper
// hen over dens overkant.
_SOFFIT_CLAD_FACE = RH_HOUSEWRAP_T + RH_COUNTER_BATTEN_T + cs_thick(RH_CLAD);

// fascia_top_offset_for() lives in config.scad — covers tagpap, eternit, polycarb.

// Rafters owned by HOUSE — left barge + V3 gable + first two inner rafters.
_HOUSE_RAFTER_XS = [
    -RH_OH_SIDE,    // left barge
    0,              // V3 gable
    600,
    1200
];

module _render_rafters_house(eh_back, palette) {
    ww = RH_HOUSE_DEPTH; sd = 95;
    y_start = -RH_OH_FRONT;
    y_end   = ww + RH_OH_BACK;
    z_start = roof_underside_for(eh_back, y_start) - RH_RAFTER_H;
    z_end   = roof_underside_for(eh_back, y_end)   - RH_RAFTER_H;
    z_v1_top = RH_BASE_H + RH_EH_FRONT;
    z_v2_top = RH_BASE_H + RH_EH_BACK;
    y_brk_f = sd / 2;
    y_brk_b = ww - sd / 2;
    BRK_W = 50; BRK_LEG = 90; BRK_T = 2;

    for (i = [0 : len(_HOUSE_RAFTER_XS) - 1]) {
        x = _HOUSE_RAFTER_XS[i];
        is_left_barge = (i == 0);

        color(pal_post(palette))
        hull() {
            translate([x, y_start, z_start])
                cube([RH_RAFTER_W, 0.01, RH_RAFTER_H]);
            translate([x, y_end - 0.01, z_end])
                cube([RH_RAFTER_W, 0.01, RH_RAFTER_H]);
        }

        if (!is_left_barge) {
            vinkelbeslag([x, y_brk_f - BRK_W/2, z_v1_top],
                         leg=BRK_LEG, thick=BRK_T, width=BRK_W,
                         orientation="-x+z");
            vinkelbeslag([x, y_brk_b - BRK_W/2, z_v2_top],
                         leg=BRK_LEG, thick=BRK_T, width=BRK_W,
                         orientation="-x+z");
        }
        // Right side bracket — all 4 house rafters get one (the next rafter
        // on the right is yard's, but its left-side bracket attaches there).
        vinkelbeslag([x + RH_RAFTER_W, y_brk_f - BRK_W/2, z_v1_top],
                     leg=BRK_LEG, thick=BRK_T, width=BRK_W,
                     orientation="+x+z");
        vinkelbeslag([x + RH_RAFTER_W, y_brk_b - BRK_W/2, z_v2_top],
                     leg=BRK_LEG, thick=BRK_T, width=BRK_W,
                     orientation="+x+z");
    }
}

// Left-side lookouts — 3 stk, between barge and V3 gable rafter.
module _render_lookouts_house(eh_back, palette) {
    LOOKOUT_LEN = RH_OH_SIDE - RH_RAFTER_W;
    LOOKOUT_YS  = [47.5, RH_HOUSE_DEPTH/2, RH_HOUSE_DEPTH - 47.5];
    color(pal_post(palette))
    for (yc = LOOKOUT_YS) {
        z_top = roof_underside_for(eh_back, yc);
        z_bot = z_top - RH_RAFTER_H;
        y_min = yc - RH_RAFTER_W/2;
        translate([-RH_OH_SIDE + RH_RAFTER_W, y_min, z_bot])
            cube([LOOKOUT_LEN, RH_RAFTER_W, RH_RAFTER_H]);
    }
}

module _soffit_panel(x0, x1, y0, y1, eh_back, palette) {
    z_top_y0 = roof_underside_for(eh_back, y0) - RH_RAFTER_H;
    z_top_y1 = roof_underside_for(eh_back, y1) - RH_RAFTER_H;
    color(pal_soffit(palette))
    polyhedron(
        points = [
            [x0, y0, z_top_y0 - SOFFIT_T],
            [x1, y0, z_top_y0 - SOFFIT_T],
            [x1, y1, z_top_y1 - SOFFIT_T],
            [x0, y1, z_top_y1 - SOFFIT_T],
            [x0, y0, z_top_y0],
            [x1, y0, z_top_y0],
            [x1, y1, z_top_y1],
            [x0, y1, z_top_y1]
        ],
        faces = [[0,1,2,3], [4,7,6,5], [0,4,5,1], [1,5,6,2], [2,6,7,3], [3,7,4,0]]
    );
}

module _render_soffit_house(eh_back, palette) {
    hl = RH_HOUSE_LEN; ww = RH_HOUSE_DEPTH;
    x_left  = -RH_OH_SIDE - RH_FASCIA_T;
    // Soffit extends to V4's yard-side face (=hl) so the partition is fully
    // tucked under the house roof eave.
    x_right = hl;
    _soffit_panel(x_left, x_right, -RH_OH_FRONT, 0, eh_back, palette);
    _soffit_panel(x_left, x_right, ww, ww + RH_OH_BACK, eh_back, palette);
    _soffit_panel(x_left, 0, 0, ww, eh_back, palette);
}

// Fascia only — no gutter / downspout. Front+back [x_left..hl] + left side.
module _render_fascia_house(eh_back, fascia_top_offset, palette) {
    hl = RH_HOUSE_LEN; ww = RH_HOUSE_DEPTH;
    drop_full = total_drop_for(eh_back);
    roof_oz   = roof_oz_for(eh_back);
    z_front_top = roof_oz + fascia_top_offset;
    z_back_top  = roof_oz - drop_full + fascia_top_offset;
    fascia_h = 140;
    fascia_t = RH_FASCIA_T;

    fx_lo = -RH_OH_SIDE - fascia_t;
    fx_hi = hl;
    y0 = -RH_OH_FRONT;
    y1 = ww + RH_OH_BACK;

    color(pal_trim(palette)) {
        translate([fx_lo, y0, z_front_top - fascia_h])
            cube([fx_hi - fx_lo, fascia_t, fascia_h]);
        translate([fx_lo, y1 - fascia_t, z_back_top - fascia_h])
            cube([fx_hi - fx_lo, fascia_t, fascia_h]);
        hull() {
            translate([fx_lo, y0, z_front_top - fascia_h])
                cube([fascia_t, 0.01, fascia_h]);
            translate([fx_lo, y1, z_back_top - fascia_h])
                cube([fascia_t, 0.01, fascia_h]);
        }
    }
}

// Sternbræt (fascia) 25×200 on the rafter tails at BOTH eaves of the gable roof
// (x = -G_OH_EAVE and x = RH_HOUSE_LEN + G_OH_EAVE). LAV STERN: overkanten
// flugter spærets overkant ved spærenden (G_STERN_TOP), så undertaget kan
// føres ud over den via tagfodsblikket. Monteres FØR undertag og lægter.
// Løber helt ud til vindskede-overliggerens yderside (±G_OH_RAKE) — de to
// vindskedebrædder er hakket ned over sternens top i hjørnet.
module _render_stern_gable(palette) {
    stern_h = G_STERN_H;   // 25×200
    y0 = -G_OH_RAKE;
    y1 = RH_HOUSE_DEPTH + G_OH_RAKE;
    for (x_face = [-G_OH_EAVE, RH_HOUSE_LEN + G_OH_EAVE]) {
        z_top = g_rafter_top_z(x_face) + G_STERN_TOP;
        x0 = x_face < G_RIDGE_X ? x_face - RH_FASCIA_T : x_face;
        color(pal_trim(palette))
        translate([x0, y0, z_top - stern_h])
            cube([RH_FASCIA_T, y1 - y0, stern_h]);
    }
}

// ---- Sofit for the gable roof. Ventilerede lameller (høvlet forskalling
// m/fas, høvlet mål G_SOFFIT_T × G_SOFFIT_W) skruet op under spærene,
// PARALLELT med tagkanten, med jævnt fordelt luftspalte. Lukket hele vejen
// rundt: begge tagfødder (spærenderne krager G_OH_EAVE ud) og begge gavle
// (udhængsspærene krager G_OH_RAKE_STRUCT ud). Insektnet på lamellernes
// overside lukker spalterne mod fugle og hvepse (REQ-008) — selve tagrummets
// ventilation sker fortsat i afstandsliste-gabet ved fodblikket
// (arbejdsplan trin 6); spalterne her lufter tagskæggets eget hulrum.
//
// Antal lameller over en bredde `span` (målt PÅ SKRÅFLADEN ved tagfoden, i Y
// ved gavlen) — så mange der giver en spalte tættest på G_SOFFIT_GAP, dog
// aldrig flere end der er plads til. Spalten fordeles derefter jævnt, så
// yderste lamel flugter sternen/vindskeden og inderste flugter væggen.
function _soffit_n(span) =
    min(floor(span / G_SOFFIT_W),
        max(1, round(span / (G_SOFFIT_W + G_SOFFIT_GAP))));
function _soffit_gap(span) =
    let (n = _soffit_n(span)) n > 1 ? (span - n * G_SOFFIT_W) / (n - 1) : 0;

// Én lamel/plade i spærplanets underside mellem x_in og x_out (samme halvtag)
// og y0..y1. Følger 35°-hældningen, tykkelsen måles lodret.
module _soffit_slab_gable(x_in, x_out, y0, y1, palette) {
    z_in  = g_rafter_bottom_z(x_in);
    z_out = g_rafter_bottom_z(x_out);
    color(pal_soffit(palette))
    hull() {
        translate([x_in,  y0, z_in  - G_SOFFIT_T]) cube([0.01, y1 - y0, G_SOFFIT_T]);
        translate([x_out, y0, z_out - G_SOFFIT_T]) cube([0.01, y1 - y0, G_SOFFIT_T]);
    }
}

// Tagfods-sofit: lameller langs Y (på tværs af spærene, så hver lamel har
// fæste i hver eneste spærende), stablet op ad skråfladen fra sternen og ind
// mod væggen. Stopper i Y ved gavlbeklædningens yderside — resten af hjørnet
// hører til gavlsofitten, der løber ubrudt hen over det.
module _render_soffit_eave(palette) {
    y0   = -_SOFFIT_CLAD_FACE;
    y1   = RH_HOUSE_DEPTH + _SOFFIT_CLAD_FACE;
    span = G_OH_EAVE / cos(G_PITCH_DEG);        // skråmål væglinje -> spærende
    n    = _soffit_n(span);
    gap  = _soffit_gap(span);
    for (i = [0 : n - 1]) {
        s0 = i * (G_SOFFIT_W + gap);            // 0 = yderst, ved sternen
        s1 = s0 + G_SOFFIT_W;
        dx0 = s0 * cos(G_PITCH_DEG);
        dx1 = s1 * cos(G_PITCH_DEG);
        _soffit_slab_gable(-G_OH_EAVE + dx0, -G_OH_EAVE + dx1, y0, y1, palette);
        _soffit_slab_gable(RH_HOUSE_LEN + G_OH_EAVE - dx1,
                           RH_HOUSE_LEN + G_OH_EAVE - dx0, y0, y1, palette);
    }
}

// Gavl-sofit: lameller langs X (op ad skråfladen, parallelt med vindskeden),
// stablet i Y fra vindskedens inderside ind mod beklædningen. Yderste lamel
// sidder under udhængsspæret, den inderste under klodserne. Kører hele vejen
// fra spærende til spærende, så den lukker tagfodshjørnet.
module _render_soffit_rake(palette) {
    span = G_OH_RAKE_STRUCT - _SOFFIT_CLAD_FACE;
    n    = _soffit_n(span);
    gap  = _soffit_gap(span);
    for (i = [0 : n - 1]) {
        a0 = i * (G_SOFFIT_W + gap);            // 0 = yderst, ved vindskeden
        a1 = a0 + G_SOFFIT_W;
        for (yb = [[-G_OH_RAKE_STRUCT, +1],
                   [RH_HOUSE_DEPTH + G_OH_RAKE_STRUCT, -1]]) {
            y0 = yb[1] > 0 ? yb[0] + a0 : yb[0] - a1;
            y1 = yb[1] > 0 ? yb[0] + a1 : yb[0] - a0;
            _soffit_slab_gable(-G_OH_EAVE, G_RIDGE_X, y0, y1, palette);
            _soffit_slab_gable(G_RIDGE_X, RH_HOUSE_LEN + G_OH_EAVE, y0, y1, palette);
        }
    }
}

module _render_soffit_gable(palette) {
    _render_soffit_eave(palette);
    _render_soffit_rake(palette);
}

// ---- Step-by-step entries for the gable/skifer roof — one per arbejdsplan
// work step, so main.scad can toggle each build stage separately.
module RenderHouseRoofSpaer(palette = DEFAULT_PALETTE) {
    RenderHouseGableSpaer(palette);
}
module RenderHouseRoofUdhaeng(palette = DEFAULT_PALETTE) {
    RenderHouseGableUdhaeng(palette);
}
module RenderHouseRoofSofit(palette = DEFAULT_PALETTE) {
    _render_soffit_gable(palette);
}
module RenderHouseRoofStern(palette = DEFAULT_PALETTE) {
    _render_stern_gable(palette);
}
module RenderHouseRoofVindskeder(palette = DEFAULT_PALETTE) {
    RenderHouseGableVindskeder(palette);
}

module RenderHouseRoof(roof_cover, palette = DEFAULT_PALETTE) {
    if (is_gable_roof(roof_cover)) {
        RenderHouseRoofSpaer(palette);
        RenderHouseRoofUdhaeng(palette);
        RenderHouseRoofSofit(palette);
        RenderHouseRoofStern(palette);
        RenderHouseRoofVindskeder(palette);
    } else {
        eh_back           = back_eave_height_for(roof_cover);
        fascia_top_offset = fascia_top_offset_for(roof_cover);
        _render_rafters_house(eh_back, palette);
        _render_lookouts_house(eh_back, palette);
        _render_soffit_house(eh_back, palette);
        _render_fascia_house(eh_back, fascia_top_offset, palette);
    }
}
