KasperBaun/RabbitHouse/src/designs/v3/tagkonstruktion_tagpap.scad

// tagkonstruktion_tagpap.scad — v3 tag: tagpap_osb cover + sternkapsler.
//
// Cover-stak fra spær-top og opefter:
//   0..18 mm    OSB plader (bærer hele coveret, sømmes på spær)
//   18..21 mm   Underpap (mekanisk fastgjort til OSB)
//   21..25 mm   Tagpap (svejset til underpap)
//   + 2 mm aluinddækning (sternkapsler) på alle 4 eaves.
// Total cover-tykkelse ~25 mm (over spær-top). Min hældning 2,5°. Passer
// til v3's 4,6° (8 % fald). DETTE ER DEFAULT-coveret.
//
// Bærende træværk (v3_spaer, v3_lookouts, v3_sofitt) og det fælles
// _v3_roof_layer-helper kommer fra tagkonstruktion_faelles.scad.

include <../../lib/defaults.scad>
include <config.scad>
use <tagkonstruktion_faelles.scad>
use <../../lib/primitives/roof.scad>

// ============================================================================
// Cover-lag konstanter — kun tagpap_osb.
// ============================================================================
OSB_T      = 18;
UNDERPAP_T = 3;
TAGPAP_T   = 4;

OSB_COLOR      = [0.78, 0.66, 0.42];
UNDERPAP_COLOR = [0.18, 0.16, 0.14];
TAGPAP_COLOR   = [0.08, 0.08, 0.08];
ALU_COLOR      = [0.78, 0.78, 0.80];

module v3_osb_daek(eh_back, palette = DEFAULT_PALETTE) {
    _v3_roof_layer(eh_back, 0, OSB_T, OSB_COLOR);
}

module v3_underpap(eh_back, palette = DEFAULT_PALETTE) {
    _v3_roof_layer(eh_back, OSB_T, UNDERPAP_T, UNDERPAP_COLOR);
}

module v3_tagpap_overlag(eh_back, palette = DEFAULT_PALETTE) {
    _v3_roof_layer(eh_back, OSB_T + UNDERPAP_T, TAGPAP_T, TAGPAP_COLOR);
}

// Sternkapsel cap-profil 35×25 mm i aluminium: glides over sternbræt-toppen
// + den oprullede tagpap-kant. 25 mm topflange matcher sternbræt-tykkelsen
// (V3_STERN_T = 25); 35 mm drop hænger ned udvendigt forbi sternbrædet.
//
// Anvendes ved alle 4 eaves. Lige profil på horisontalt front/bag,
// skrå profil på sloped venstre/højre.
//
// Sternbræt-placering (efter at v3_tagkonstruktion_tagpap kalder fascia med
// overhang_* + V3_STERN_T): sternbrædderne sidder UDVENDIGT på spær-endefladerne.
//   • Front sternbræt outer face = Y = -V3_OH_FRONT - V3_STERN_T,
//                       inner face = Y = -V3_OH_FRONT (spær-endeflade).
//   • Bag sternbræt   outer face = Y = ww + V3_OH_BACK + V3_STERN_T.
//   • Venstre sternbræt outer face = X = -V3_OH_SIDE - V3_STERN_T.
//   • Højre sternbræt   outer face = X = ll + V3_OH_SIDE + V3_STERN_T.
//
//   sternbraet_top_offset = z-offset fra v3_roof_oz_for(eh_back) til
//                           sternbræt-toppen (= cover_thick + lip).
//                           Sternbræt-toppen sidder altid over cover-toppen
//                           med en lille kant (lip) på 7 mm.
module v3_sternkapsler(eh_back, sternbraet_top_offset, palette = DEFAULT_PALETTE) {
    ll = V3_LENGTH; ww = V3_WIDTH;
    drop_full = v3_total_drop_for(eh_back);
    roof_oz   = v3_roof_oz_for(eh_back);
    z_front = roof_oz + sternbraet_top_offset;                  // z @ y=-OH_FRONT
    z_back  = roof_oz - drop_full + sternbraet_top_offset;      // z @ y=ww+OH_BACK

    CAP_W    = V3_STERN_T;  // 25 mm cap-bredde (matcher sternbræt-top)
    CAP_DROP = 35;          // 35 mm drop udvendigt
    CAP_T    = 2;           // alu-tykkelse

    // Sternbræt yder-flader (= cap topflange yder-kanter).
    y_front_outer = -V3_OH_FRONT - V3_STERN_T;
    y_back_outer  = ww + V3_OH_BACK + V3_STERN_T;
    x_left_outer  = -V3_OH_SIDE - V3_STERN_T;
    x_right_outer = ll + V3_OH_SIDE + V3_STERN_T;

    color(ALU_COLOR) {
        // FRONT eave — topflange ligger over sternbræt-top (Y= y_front_outer..-V3_OH_FRONT).
        // Strækker sig over hele front-sternbrættets X-spænd (inkl. de sidevendte
        // sternbrædders bredde) så hjørnerne er dækkede.
        translate([x_left_outer, y_front_outer, z_front])
            cube([x_right_outer - x_left_outer, V3_STERN_T, CAP_T]);
        // Outer drop hænger udvendigt forbi sternbræt-front-fladen.
        translate([x_left_outer, y_front_outer - CAP_T, z_front - CAP_DROP])
            cube([x_right_outer - x_left_outer, CAP_T, CAP_DROP + CAP_T]);

        // BAG eave
        translate([x_left_outer, ww + V3_OH_BACK, z_back])
            cube([x_right_outer - x_left_outer, V3_STERN_T, CAP_T]);
        translate([x_left_outer, y_back_outer, z_back - CAP_DROP])
            cube([x_right_outer - x_left_outer, CAP_T, CAP_DROP + CAP_T]);

        // VENSTRE side (skrå cap der følger tagets hældning).
        // Topflange dækker sternbræt-top i X=[x_left_outer, -V3_OH_SIDE].
        hull() {
            translate([x_left_outer, y_front_outer, z_front])
                cube([V3_STERN_T, 0.01, CAP_T]);
            translate([x_left_outer, y_back_outer - 0.01, z_back])
                cube([V3_STERN_T, 0.01, CAP_T]);
        }
        // Outer drop hænger udvendigt for venstre sternbræts yder-flade.
        hull() {
            translate([x_left_outer - CAP_T, y_front_outer, z_front - CAP_DROP])
                cube([CAP_T, 0.01, CAP_DROP + CAP_T]);
            translate([x_left_outer - CAP_T, y_back_outer - 0.01, z_back - CAP_DROP])
                cube([CAP_T, 0.01, CAP_DROP + CAP_T]);
        }

        // HØJRE side
        hull() {
            translate([ll + V3_OH_SIDE, y_front_outer, z_front])
                cube([V3_STERN_T, 0.01, CAP_T]);
            translate([ll + V3_OH_SIDE, y_back_outer - 0.01, z_back])
                cube([V3_STERN_T, 0.01, CAP_T]);
        }
        hull() {
            translate([x_right_outer, y_front_outer, z_front - CAP_DROP])
                cube([CAP_T, 0.01, CAP_DROP + CAP_T]);
            translate([x_right_outer, y_back_outer - 0.01, z_back - CAP_DROP])
                cube([CAP_T, 0.01, CAP_DROP + CAP_T]);
        }
    }
}

module v3_cover_tagpap_osb(eh_back, palette = DEFAULT_PALETTE) {
    v3_osb_daek(eh_back, palette);
    v3_underpap(eh_back, palette);
    v3_tagpap_overlag(eh_back, palette);
    // Sternkapsler kaldes fra v3_tagkonstruktion_tagpap (de sidder på sternbræt-top,
    // ikke direkte på coveret).
}
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
